franrobots/RescueMaze_FranRobots_WorldWide/Docs/Media/Teamwork_Timeline.png

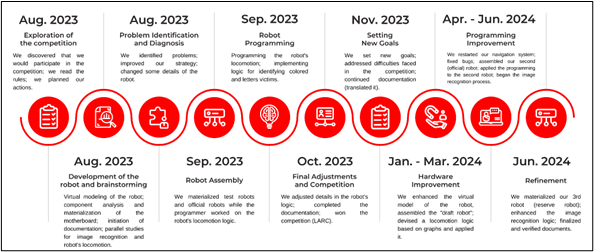
Docs/Media/Teamwork_Timeline.png
