franrobots/RescueMaze_FranRobots_WorldWide/Docs/Media/Trello_Repository.png

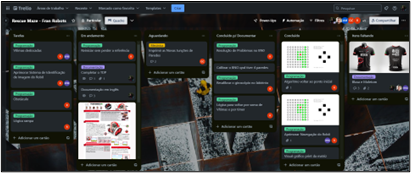
Docs/Media/Trello_Repository.png
