franrobots/RescueMaze_FranRobots_WorldWide/Electronics/Media/MotherBoard/Motherboard_3D_EasyEDA.png

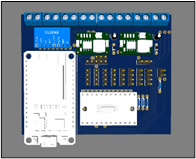
Electronics/Media/MotherBoard/Motherboard_3D_EasyEDA.png
