franrobots/RescueMaze_FranRobots_WorldWide/Electronics/Media/Reflective/Color Sensor Board/3D_Model_ColorSensorBoard.jpeg

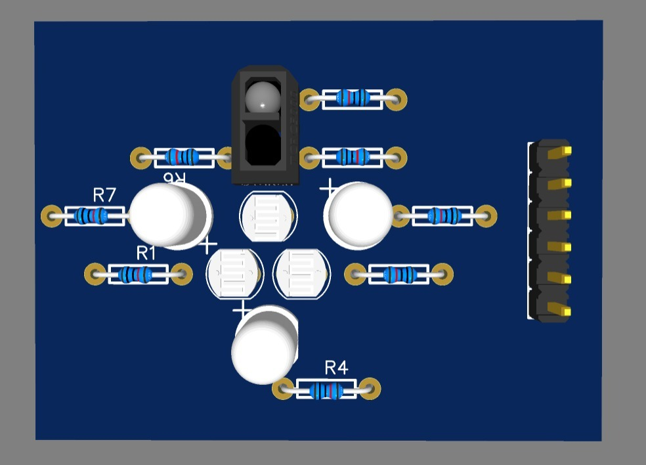
Electronics/Media/Reflective/Color Sensor Board/3D_Model_ColorSensorBoard.jpeg
