franrobots/RescueMaze_FranRobots_WorldWide/Electronics/Media/Reflective/Color Sensor Board/PCB_Layout_ColorSensorBoard.jpeg

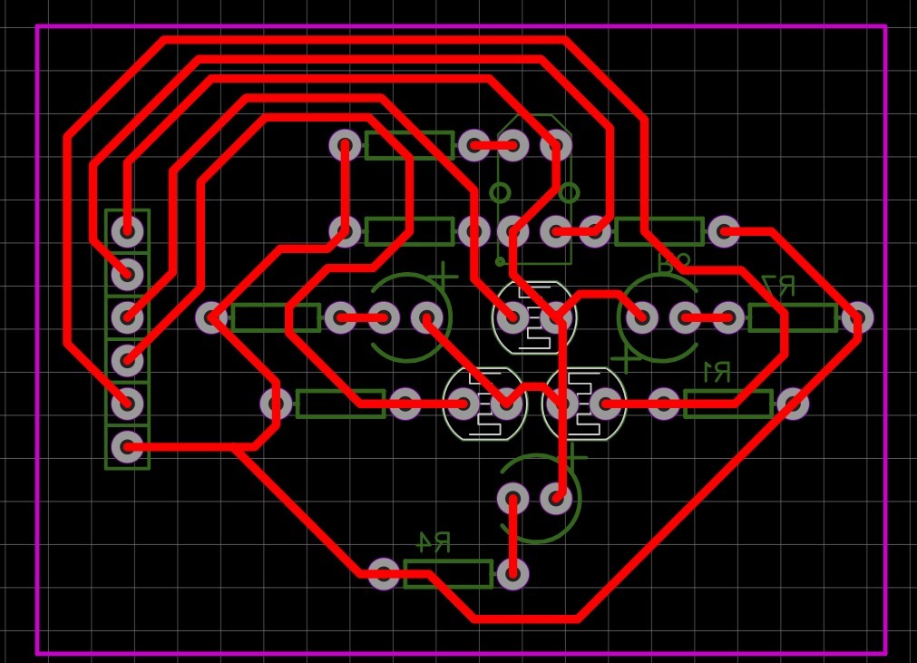
Electronics/Media/Reflective/Color Sensor Board/PCB_Layout_ColorSensorBoard.jpeg
