franrobots/RescueMaze_FranRobots_WorldWide/Mechanics/Media/3D/Anti-Rollover_Part.jpeg

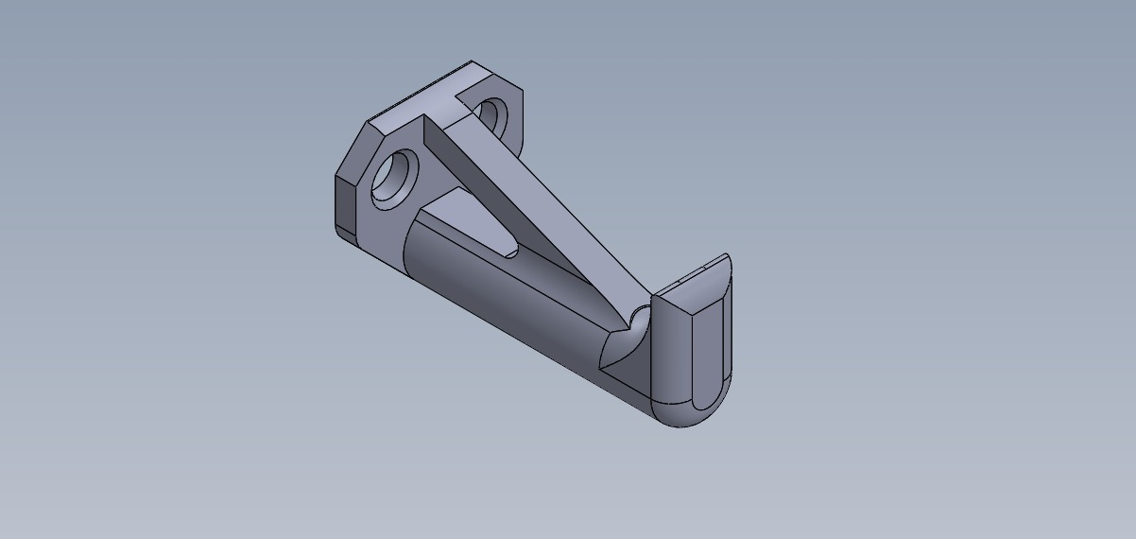
Mechanics/Media/3D/Anti-Rollover_Part.jpeg
