franrobots/RescueMaze_FranRobots_WorldWide/Mechanics/Media/Ilustrations/CrankShaftMechanism_Ilustration.jpg

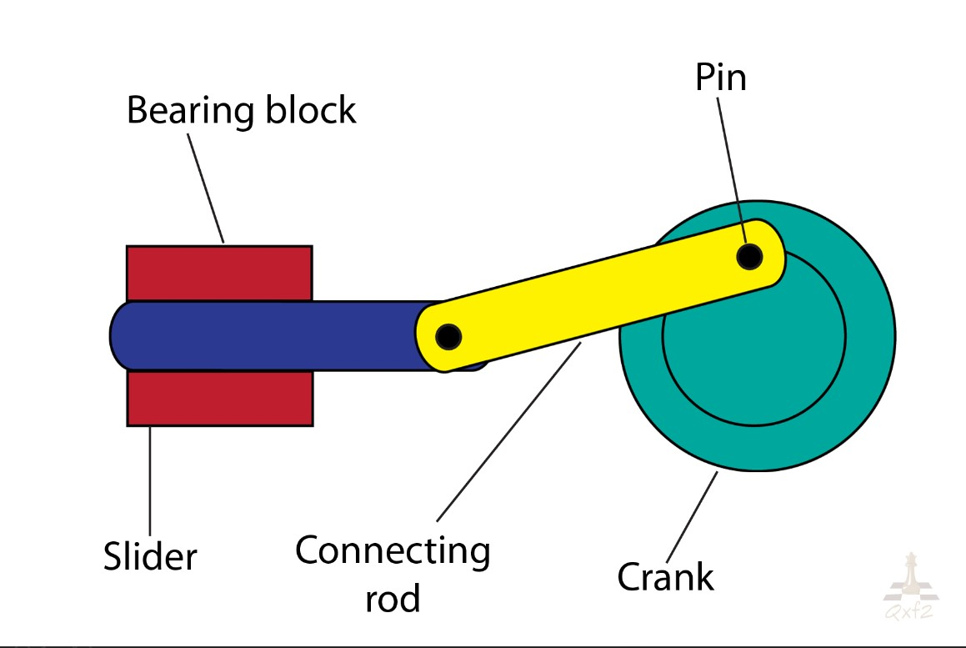
Mechanics/Media/Ilustrations/CrankShaftMechanism_Ilustration.jpg
