franrobots/RescueMaze_FranRobots_WorldWide/Mechanics/Media/Ilustrations/Trigger_Diagram.png

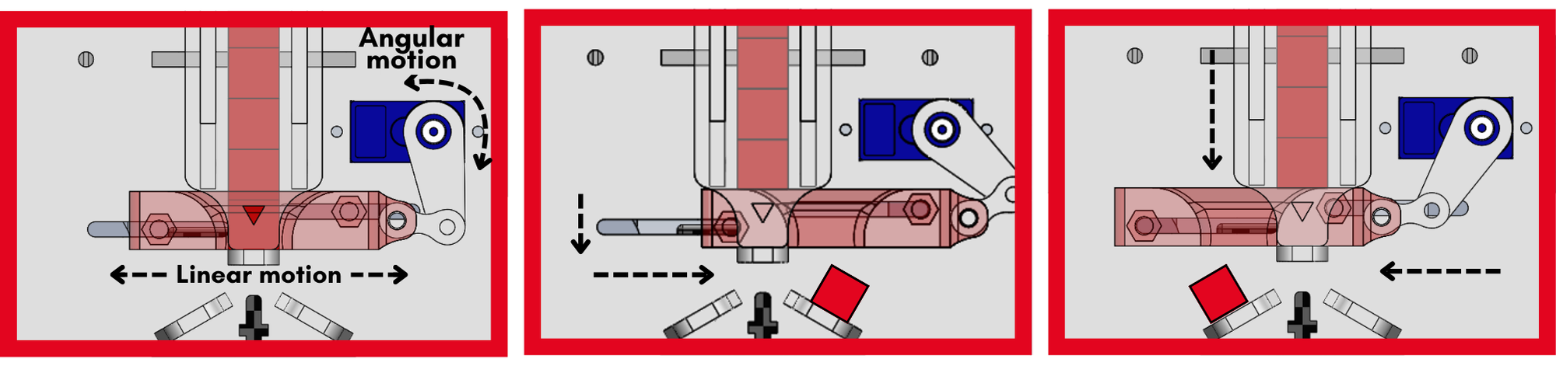
Mechanics/Media/Ilustrations/Trigger_Diagram.png
