franrobots/RescueMaze_FranRobots_WorldWide/Mechanics/Renderings/MazeRobot_Isometric_Back Render 3840x2160.JPG

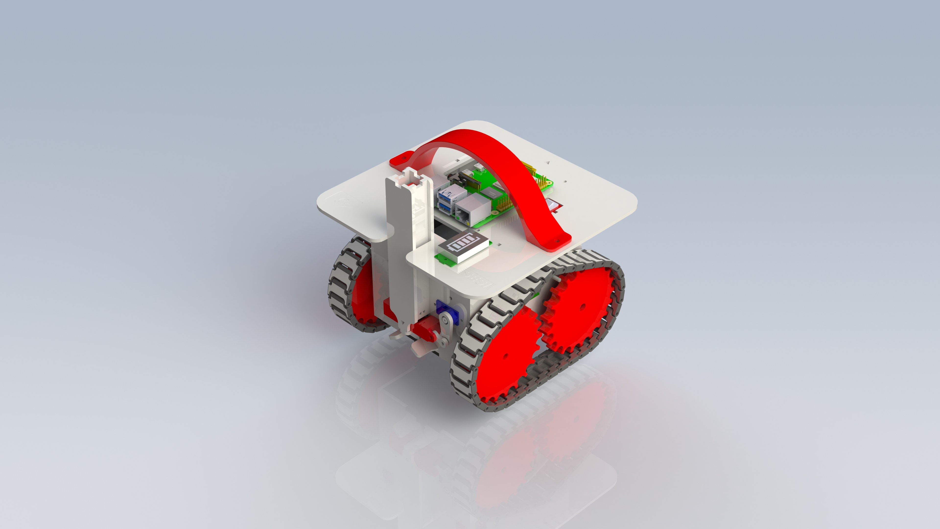
Mechanics/Renderings/MazeRobot_Isometric_Back Render 3840x2160.JPG
