franrobots/RescueMaze_FranRobots_WorldWide/Mechanics/Renderings/MazeRobot_Isometric_Front Render 3840x2160.JPG

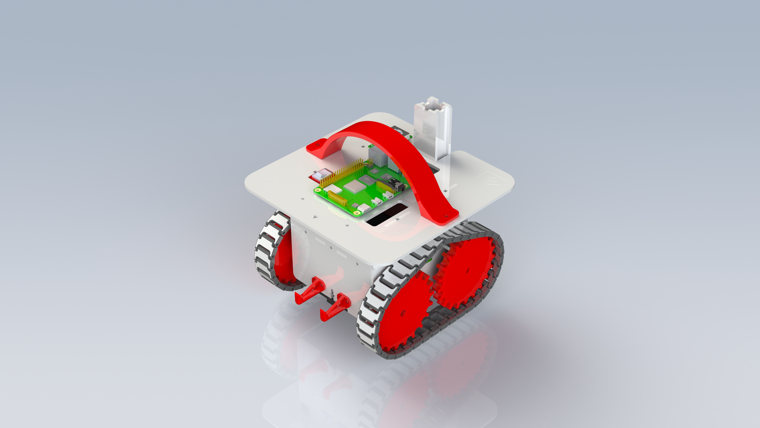
Mechanics/Renderings/MazeRobot_Isometric_Front Render 3840x2160.JPG
