franrobots/RescueMaze_FranRobots_WorldWide/Mechanics/Renderings/MazeRobot_Side Render 3840x2160.JPG

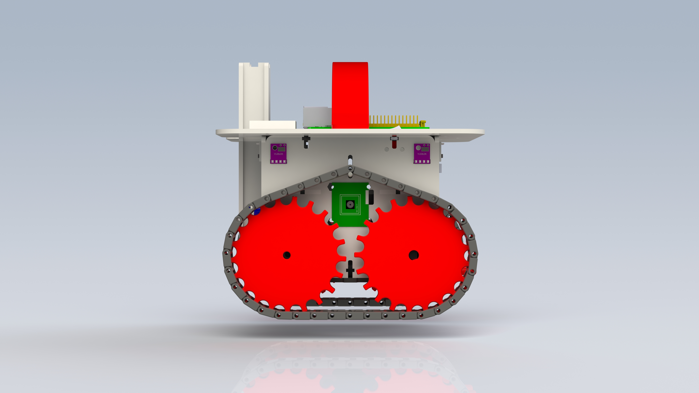
Mechanics/Renderings/MazeRobot_Side Render 3840x2160.JPG
