franrobots/RescueMaze_FranRobots_WorldWide/Programming/Media/Flowcharts/Flowchart_analysis_of_tile_colors__decision_process__action_taking.png

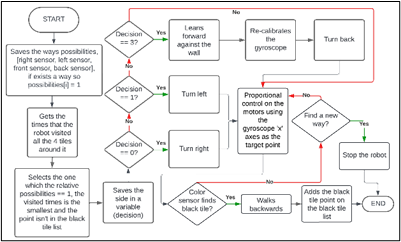
Programming/Media/Flowcharts/Flowchart_analysis_of_tile_colors__decision_process__action_taking.png
