franrobots/RescueMaze_FranRobots_WorldWide/Programming/Media/Flowcharts/Flowchart_interruption_process.png

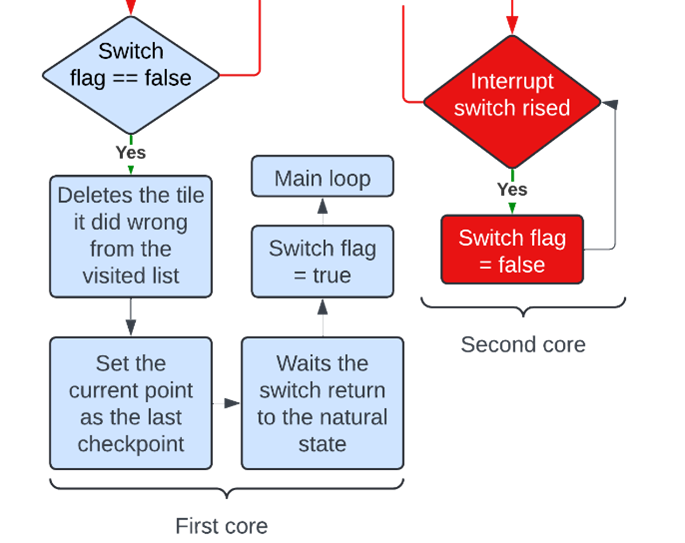
Programming/Media/Flowcharts/Flowchart_interruption_process.png
