franrobots/RescueMaze_FranRobots_WorldWide/Programming/Media/Flowcharts/Flowchart_our_library.png

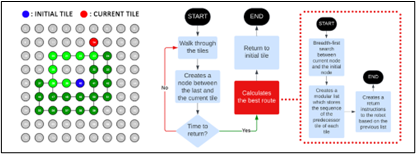
Programming/Media/Flowcharts/Flowchart_our_library.png
