franrobots/RescueMaze_FranRobots_WorldWide/Programming/Media/Flowcharts/Flowchart_victim_segregation_and_classification.png

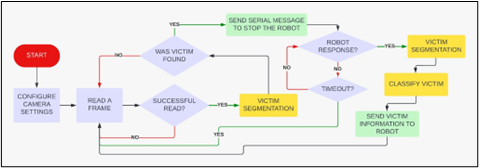
Programming/Media/Flowcharts/Flowchart_victim_segregation_and_classification.png
