franrobots/RescueMaze_FranRobots_WorldWide/Programming/Media/Picture_victim_segregation_and_classification.png

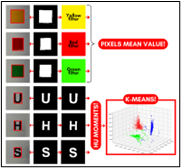
Programming/Media/Picture_victim_segregation_and_classification.png
