franrobots/RescueMaze_FranRobots_WorldWide/Mechanics/3D Printing Prices and Specs./Price and Printing Specs. - 2x Anti-Rollover Parts.png

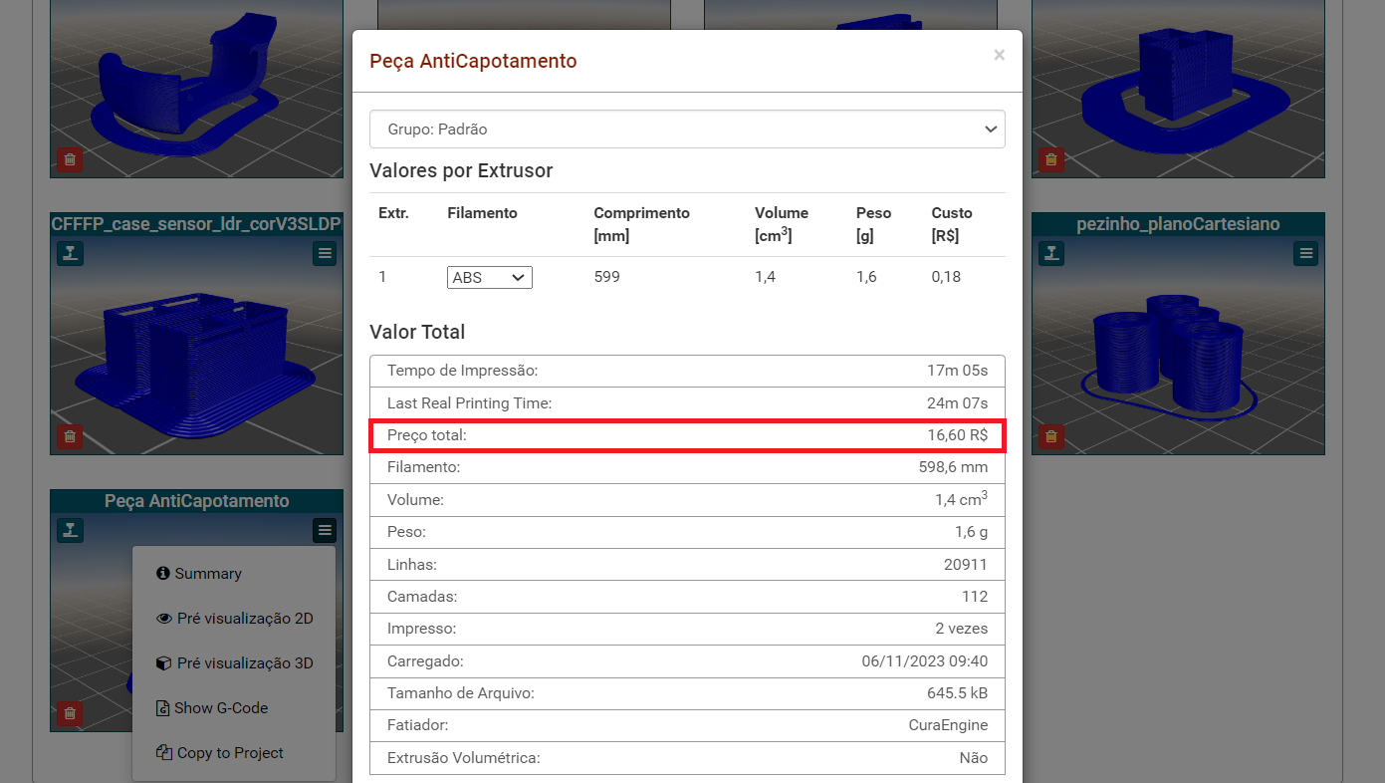
Mechanics/3D Printing Prices and Specs./Price and Printing Specs. - 2x Anti-Rollover Parts.png
