franrobots/RescueMaze_FranRobots_WorldWide/Mechanics/Robot´s 3D Models/Componentes/Parafusos e Porcas/Porcas/Porca M3.STEP

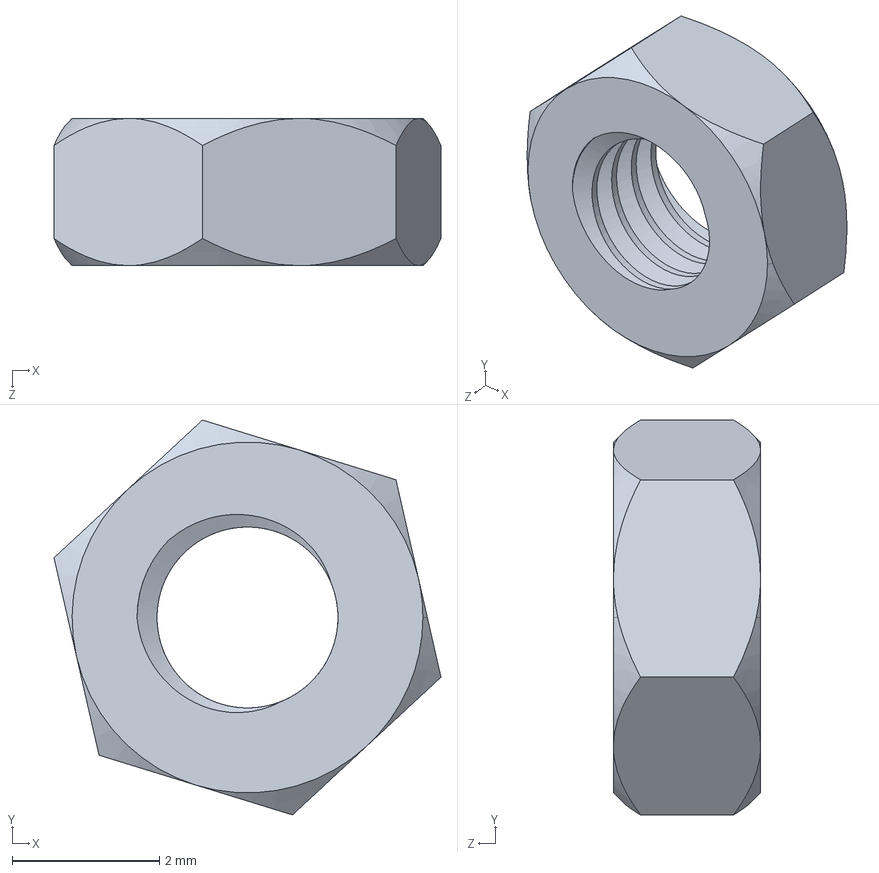
[picture p41: CAD file, 2024-06-11]
Mechanics/Robot´s 3D Models/Componentes/Parafusos e Porcas/Porcas/Porca M3.STEP
5.26 x 5.36 x 2.00 mm
