franrobots/RescueMaze_FranRobots_WorldWide/Mechanics/Robot´s 3D Models/Componentes/Placa de Refletância/Case LDR Tripla.SLDPRT

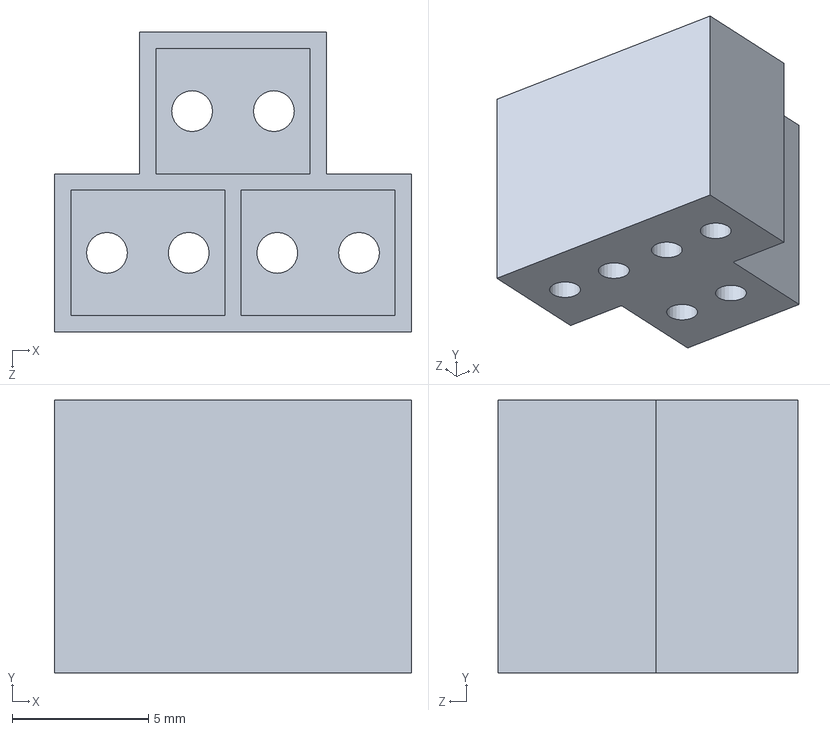
[picture p42: CAD file, 2024-06-19]
Mechanics/Robot´s 3D Models/Componentes/Placa de Refletância/Case LDR Tripla.SLDPRT
13.1 x 10.0 x 11.0 mm
