franrobots/RescueMaze_FranRobots_WorldWide/Mechanics/Robot´s 3D Models/Componentes/Placa Mãe - Robô Maze/Conectores/Barras Pinada Fêmea/19-Pin Header - Female - 2.54mm.STEP

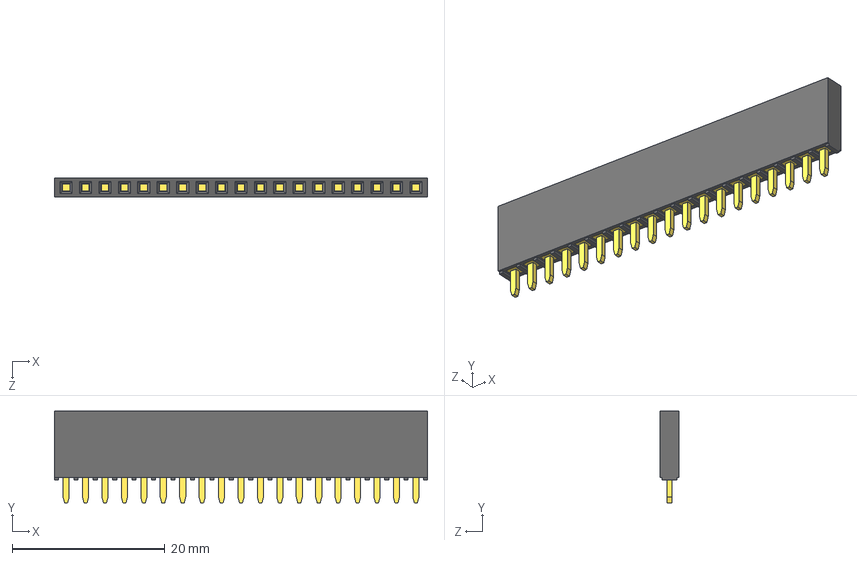
[picture p43: CAD file, 2024-06-19]
Mechanics/Robot´s 3D Models/Componentes/Placa Mãe - Robô Maze/Conectores/Barras Pinada Fêmea/19-Pin Header - Female - 2.54mm.STEP
48.8 x 12.0 x 2.50 mm
