franrobots/RescueMaze_FranRobots_WorldWide/Mechanics/Robot´s 3D Models/Componentes/Placa Mãe - Robô Maze/Conectores/Barras Pinada Macho/1-Pin Header - Male - 2.54mm/1-Pin Header - Male - 2.54mm.STEP

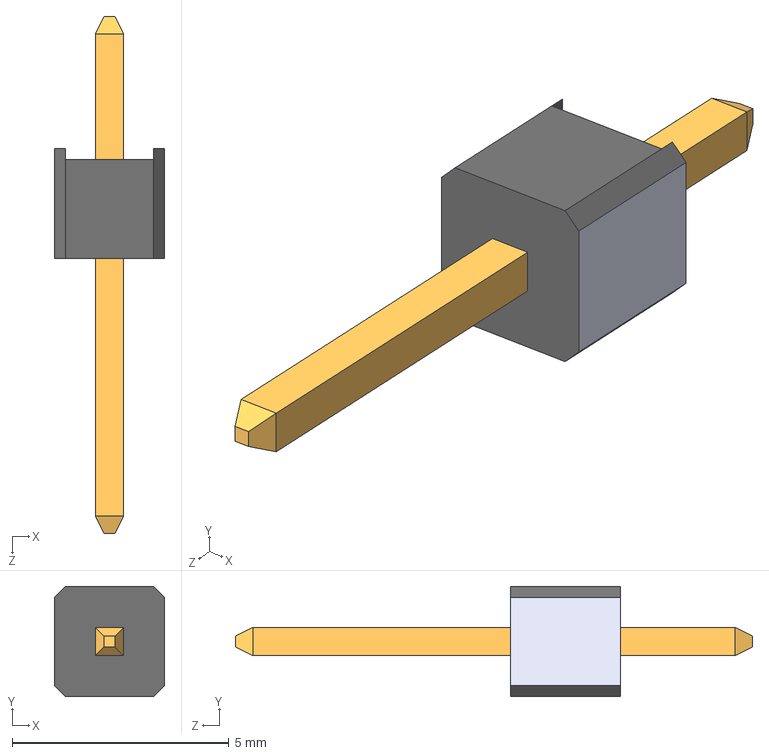
[picture p44: CAD file, 2024-06-11]
Mechanics/Robot´s 3D Models/Componentes/Placa Mãe - Robô Maze/Conectores/Barras Pinada Macho/1-Pin Header - Male - 2.54mm/1-Pin Header - Male - 2.54mm.STEP
2.54 x 2.54 x 11.9 mm
