franrobots/RescueMaze_FranRobots_WorldWide/Mechanics/Robot´s 3D Models/Componentes/Placa Mãe - Robô Maze/Conectores/Barras Pinada Macho/3-Pin Header - Male - 2.54mm.step

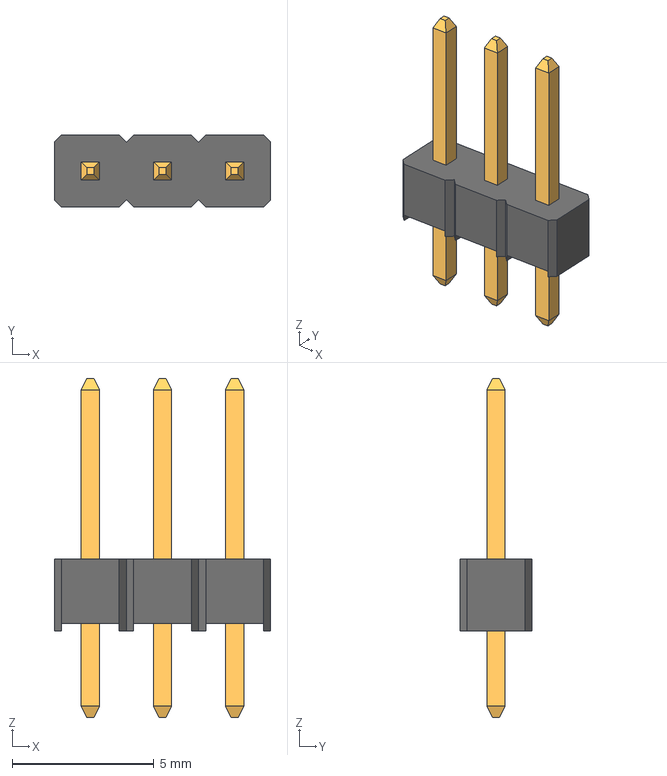
[picture p45: CAD file, 2024-06-11]
Mechanics/Robot´s 3D Models/Componentes/Placa Mãe - Robô Maze/Conectores/Barras Pinada Macho/3-Pin Header - Male - 2.54mm.step
7.62 x 2.54 x 11.9 mm
