franrobots/RescueMaze_FranRobots_WorldWide/Mechanics/Robot´s 3D Models/Componentes/Placa Mãe - Robô Maze/Conectores/Bornes/2 PIN - DG306-5 - PITCH 5 mm.stp

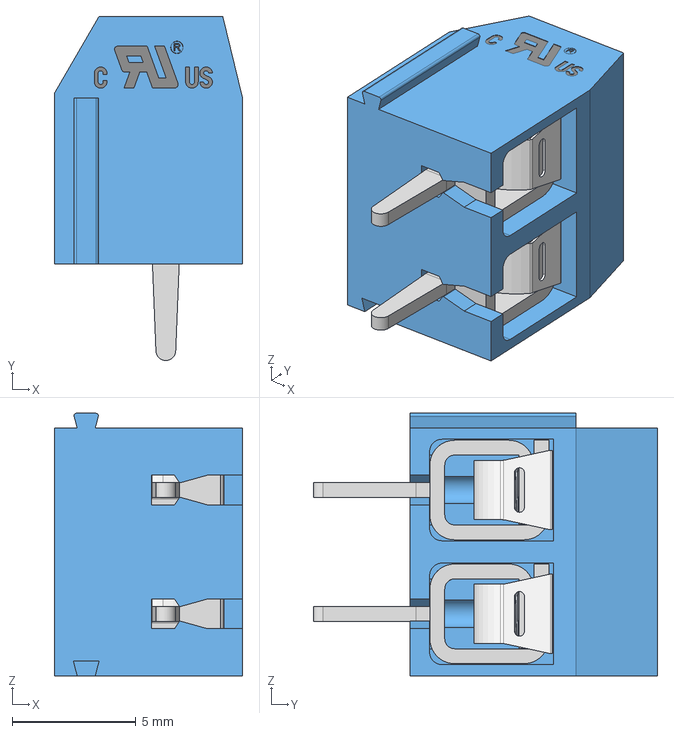
[picture p46: CAD file, 2024-06-19]
Mechanics/Robot´s 3D Models/Componentes/Placa Mãe - Robô Maze/Conectores/Bornes/2 PIN - DG306-5 - PITCH 5 mm.stp
7.60 x 13.9 x 10.6 mm
