franrobots/RescueMaze_FranRobots_WorldWide/Mechanics/Robot´s 3D Models/Componentes/Placa Mãe - Robô Maze/Placa Ilhada 90x70.SLDPRT

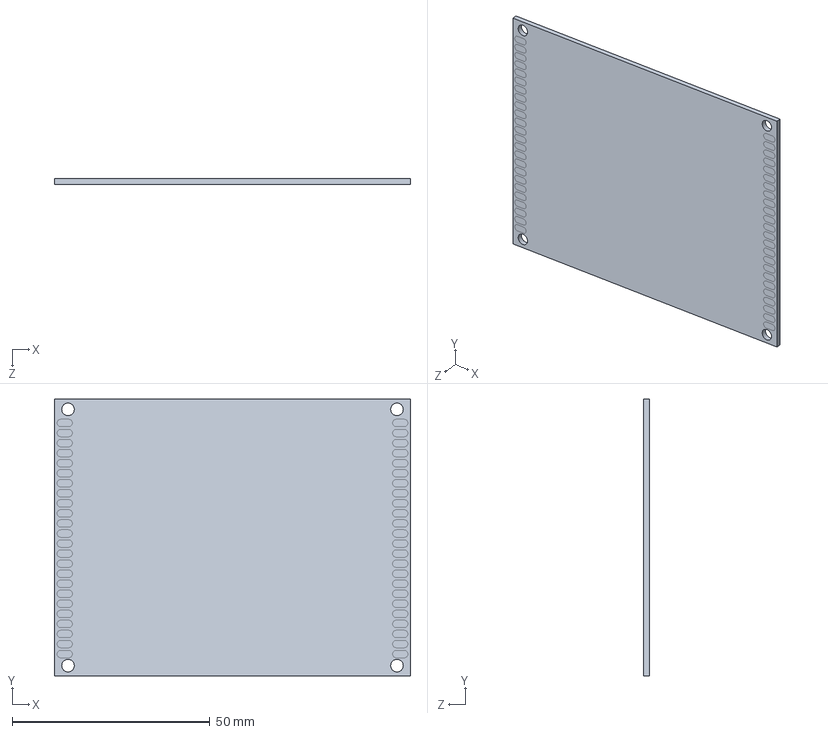
[picture p47: CAD file, 2024-06-19]
Mechanics/Robot´s 3D Models/Componentes/Placa Mãe - Robô Maze/Placa Ilhada 90x70.SLDPRT
90.0 x 70.0 x 1.42 mm
