franrobots/RescueMaze_FranRobots_WorldWide/Mechanics/Robot´s 3D Models/Componentes/Servo Motor/SG90 - Micro Servo 9g - Tower Pro.SLDPRT

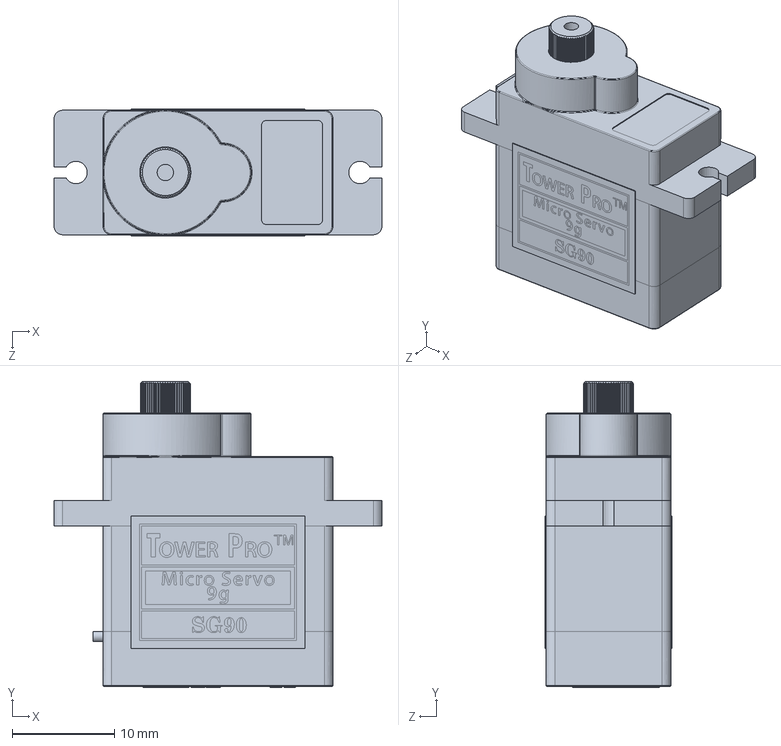
[picture p48: CAD file, 2024-06-19]
Mechanics/Robot´s 3D Models/Componentes/Servo Motor/SG90 - Micro Servo 9g - Tower Pro.SLDPRT
32.1 x 30.0 x 12.4 mm
