franrobots/RescueMaze_FranRobots_WorldWide/Mechanics/Robot´s 3D Models/Componentes/Switchs/tugas uts rocker switch.SLDPRT

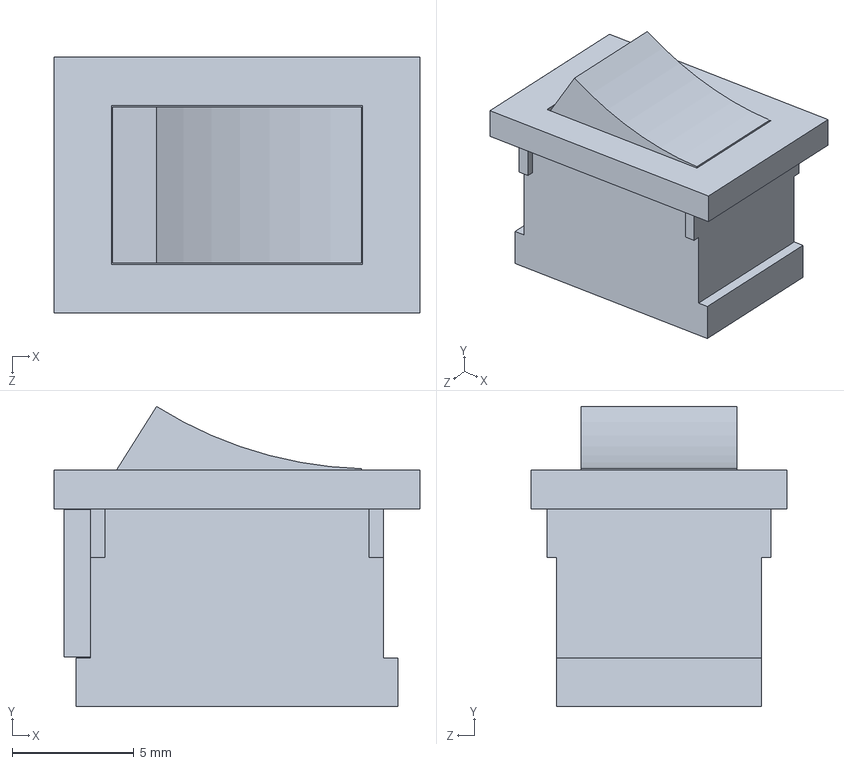
[picture p49: CAD file, 2024-06-19]
Mechanics/Robot´s 3D Models/Componentes/Switchs/tugas uts rocker switch.SLDPRT
15.0 x 12.3 x 10.5 mm
