franrobots/RescueMaze_FranRobots_WorldWide/Mechanics/Robot´s 3D Models/Disparador/Disparador Tapete/Conector Servo Manivela.SLDPRT

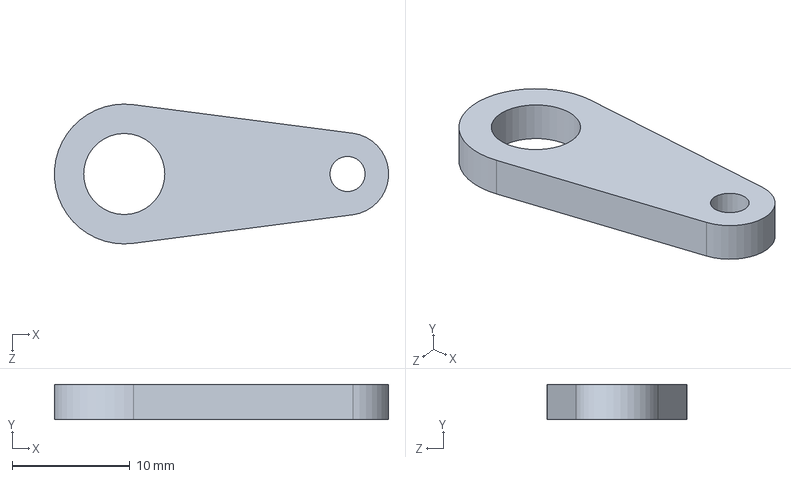
[picture p50: CAD file, 2024-06-19]
Mechanics/Robot´s 3D Models/Disparador/Disparador Tapete/Conector Servo Manivela.SLDPRT
28.4 x 3.00 x 11.9 mm
