franrobots/RescueMaze_FranRobots_WorldWide/Mechanics/Robot´s 3D Models/Disparador/Estoque Disparador/Parede Traseira - Estoque Disparador.SLDPRT

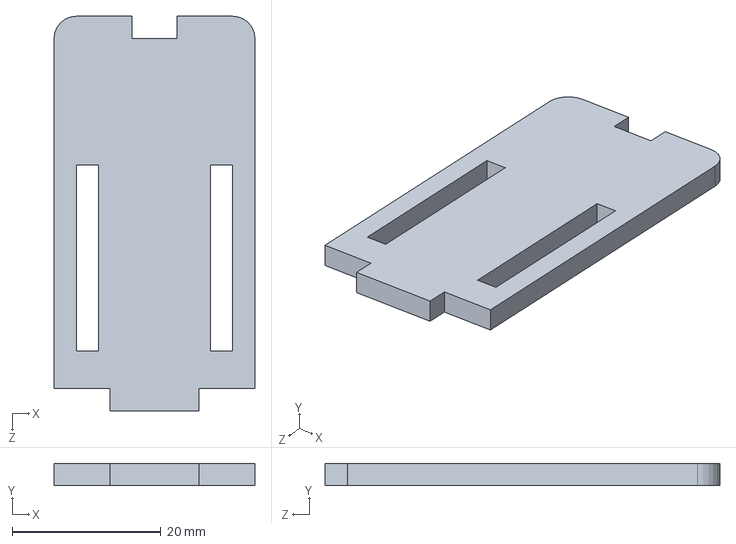
[picture p51: CAD file, 2024-06-19]
Mechanics/Robot´s 3D Models/Disparador/Estoque Disparador/Parede Traseira - Estoque Disparador.SLDPRT
27.0 x 3.00 x 53.0 mm
