franrobots/RescueMaze_FranRobots_WorldWide/Mechanics/Robot´s 3D Models/Disparador/Extensor Estoque Kits.SLDPRT

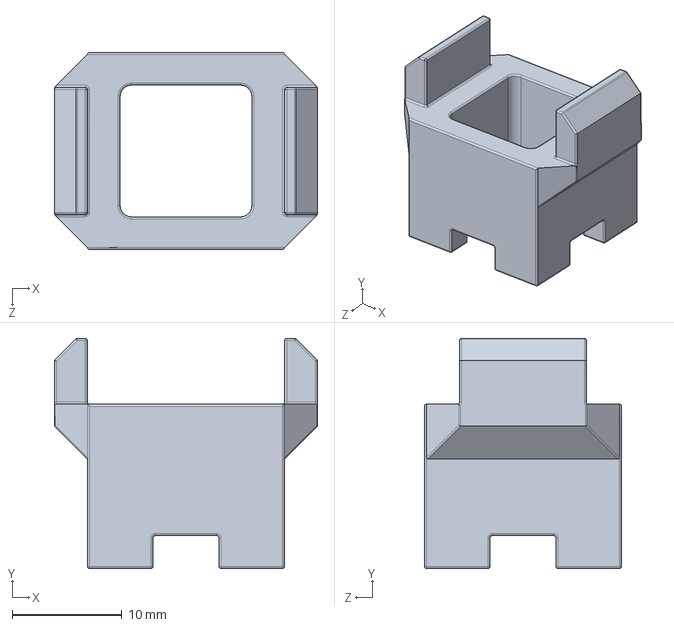
[picture p52: CAD file, 2024-06-11]
Mechanics/Robot´s 3D Models/Disparador/Extensor Estoque Kits.SLDPRT
24.0 x 21.0 x 18.0 mm
