franrobots/RescueMaze_FranRobots_WorldWide/Mechanics/Robot´s 3D Models/Lateral Direita - Maze.SLDPRT

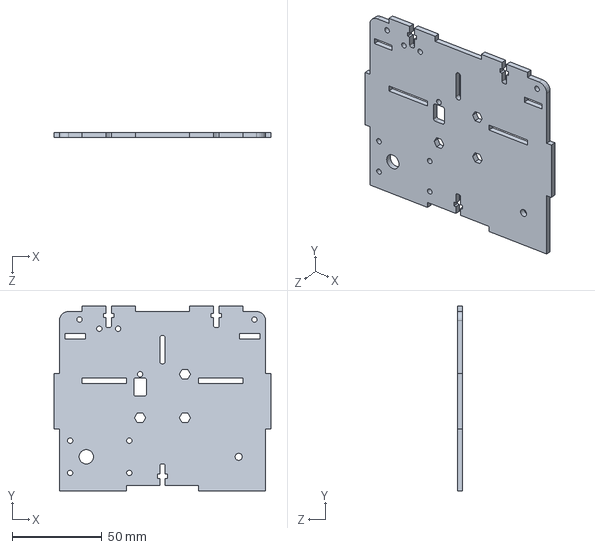
[picture p53: CAD file, 2024-06-21]
Mechanics/Robot´s 3D Models/Lateral Direita - Maze.SLDPRT
121.0 x 103.0 x 3.00 mm
