franrobots/RescueMaze_FranRobots_WorldWide/Mechanics/Robot´s 3D Models/Pista/Kit de Resgate.SLDPRT

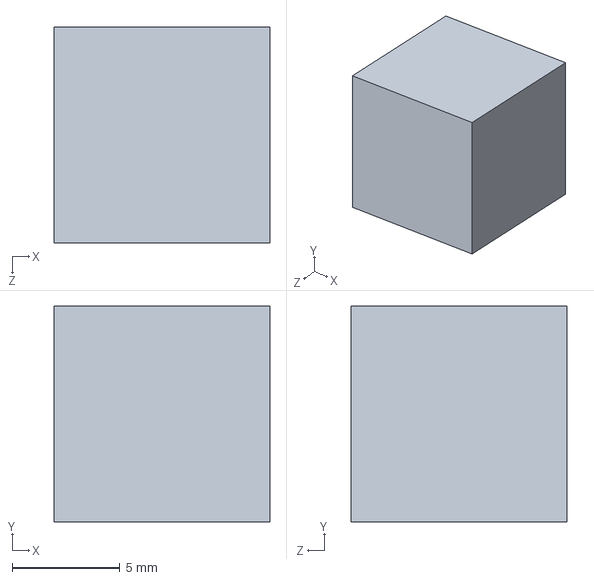
[picture p54: CAD file, 2024-06-19]
Mechanics/Robot´s 3D Models/Pista/Kit de Resgate.SLDPRT
10.0 x 10.0 x 10.0 mm
