franrobots/RescueMaze_FranRobots_WorldWide/Mechanics/Robot´s 3D Models/Rodas e esteiras/Dentes Esteira/Dente Esteira - Engrenagem.SLDPRT

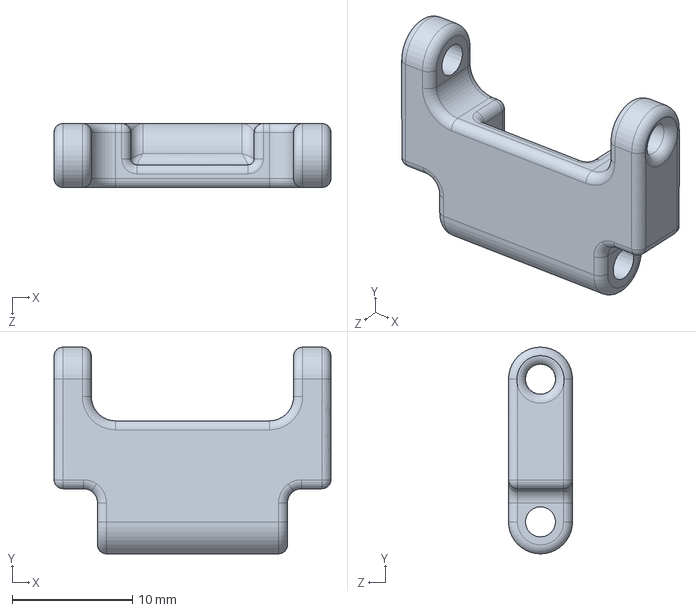
[picture p55: CAD file, 2024-06-19]
Mechanics/Robot´s 3D Models/Rodas e esteiras/Dentes Esteira/Dente Esteira - Engrenagem.SLDPRT
23.0 x 17.2 x 5.32 mm
