franrobots/RescueMaze_FranRobots_WorldWide/Mechanics/Robot´s 3D Models/Rodas e esteiras/Rodas/7988 - Atual/Engrenagem Movida Reduzida - Passo 11,92 7988.SLDPRT

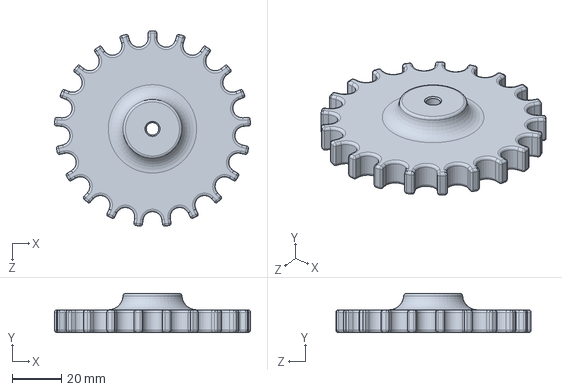
[picture p56: CAD file, 2024-06-19]
Mechanics/Robot´s 3D Models/Rodas e esteiras/Rodas/7988 - Atual/Engrenagem Movida Reduzida - Passo 11,92 7988.SLDPRT
79.8 x 15.9 x 79.6 mm
