franrobots/RescueMaze_FranRobots_WorldWide/Mechanics/Robot´s 3D Models/Componentes/Bateria/PDB XT60 PLUG.SLDPRT

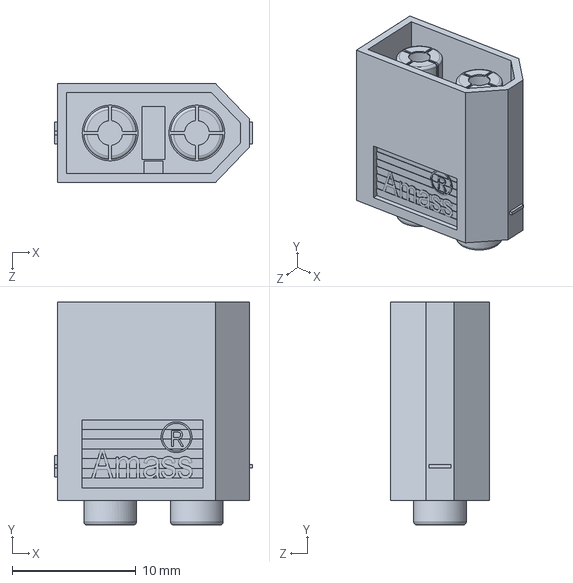
[picture p57: CAD file, 2024-06-11]
Mechanics/Robot´s 3D Models/Componentes/Bateria/PDB XT60 PLUG.SLDPRT
16.0 x 18.0 x 8.00 mm
