franrobots/RescueMaze_FranRobots_WorldWide/Mechanics/Robot´s 3D Models/Componentes/Câmera/Raspberry Cam.step

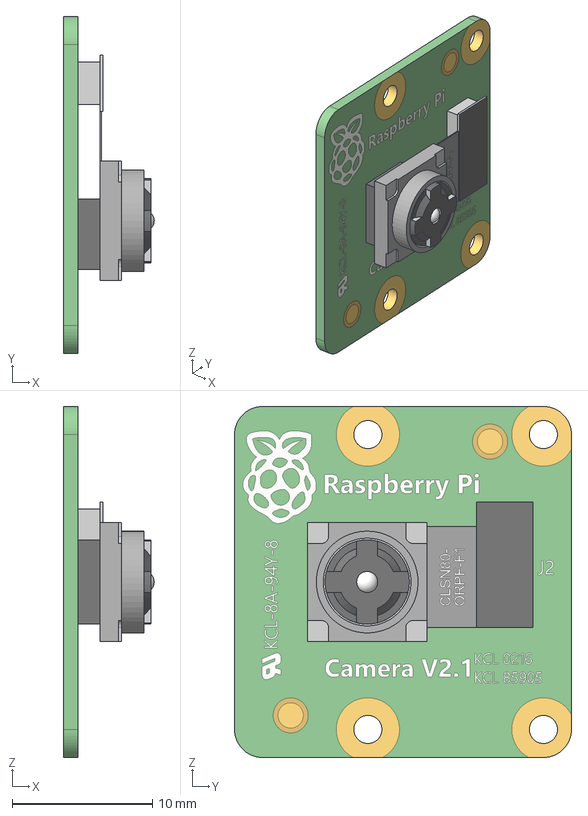
[picture p58: CAD file, 2024-06-11]
Mechanics/Robot´s 3D Models/Componentes/Câmera/Raspberry Cam.step
6.45 x 24.0 x 25.0 mm
