franrobots/RescueMaze_FranRobots_WorldWide/Mechanics/Robot´s 3D Models/Componentes/Encoder/Encoder Original/Encoder Motor.SLDPRT

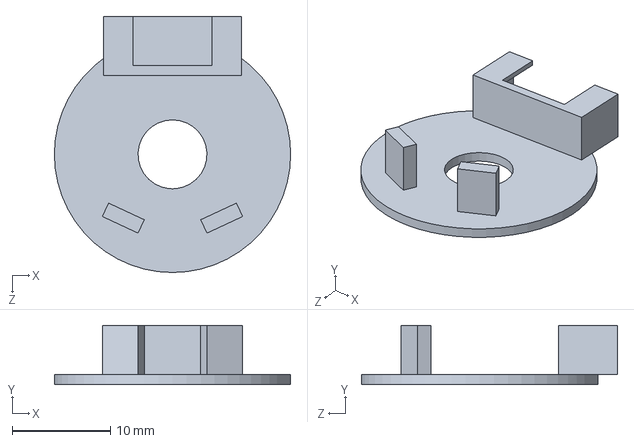
[picture p59: CAD file, 2024-06-19]
Mechanics/Robot´s 3D Models/Componentes/Encoder/Encoder Original/Encoder Motor.SLDPRT
24.0 x 6.00 x 26.0 mm
