franrobots/RescueMaze_FranRobots_WorldWide/Mechanics/Robot´s 3D Models/Componentes/GY-VL53/Adaptador GY_VL53 LDK-1XV2.SLDPRT

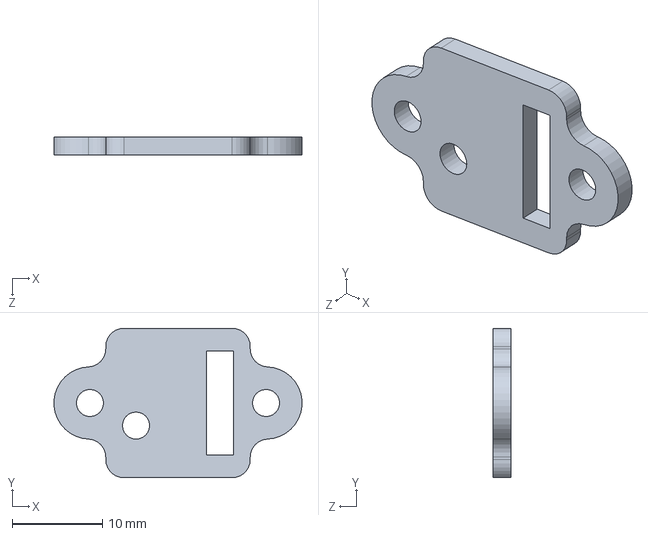
[picture p60: CAD file, 2024-06-19]
Mechanics/Robot´s 3D Models/Componentes/GY-VL53/Adaptador GY_VL53 LDK-1XV2.SLDPRT
27.5 x 16.6 x 2.00 mm
