franrobots/RescueMaze_FranRobots_WorldWide/Mechanics/Robot´s 3D Models/Componentes/Motor DC - MJ TEK8 - 12v 100 RPM.SLDPRT

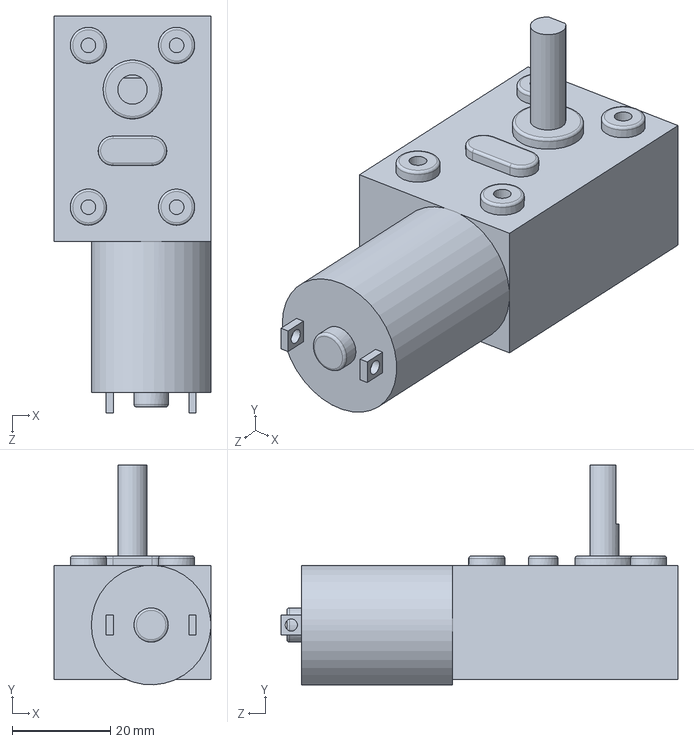
[picture p61: CAD file, 2024-06-19]
Mechanics/Robot´s 3D Models/Componentes/Motor DC - MJ TEK8 - 12v 100 RPM.SLDPRT
32.0 x 44.8 x 81.0 mm
