franrobots/RescueMaze_FranRobots_WorldWide/Mechanics/Robot´s 3D Models/Componentes/Parafusos e Porcas/Arruelas/Arruela M3.SLDPRT

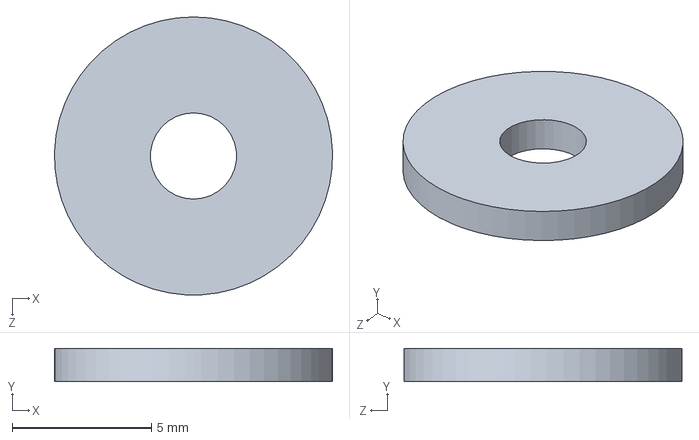
[picture p62: CAD file, 2024-06-19]
Mechanics/Robot´s 3D Models/Componentes/Parafusos e Porcas/Arruelas/Arruela M3.SLDPRT
10.00 x 1.20 x 10.0 mm
