franrobots/RescueMaze_FranRobots_WorldWide/Mechanics/Robot´s 3D Models/Componentes/Parafusos e Porcas/Parafusos/Parafuso M3 Fuso.SLDPRT

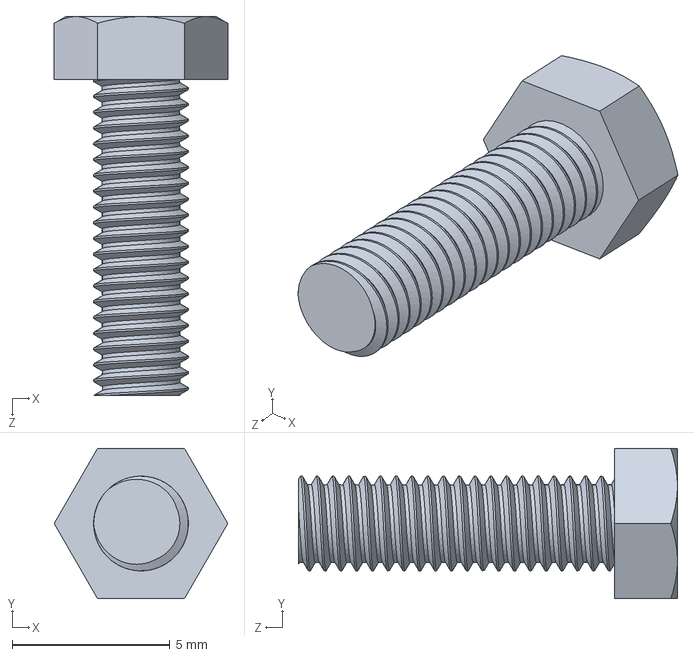
[picture p63: CAD file, 2024-06-11]
Mechanics/Robot´s 3D Models/Componentes/Parafusos e Porcas/Parafusos/Parafuso M3 Fuso.SLDPRT
5.50 x 4.76 x 12.0 mm
