franrobots/RescueMaze_FranRobots_WorldWide/Mechanics/Robot´s 3D Models/Componentes/Parafusos e Porcas/Porcas/Porca M4.stp

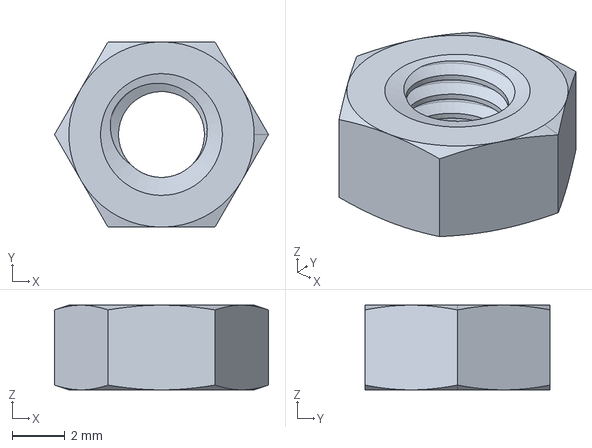
[picture p64: CAD file, 2024-06-11]
Mechanics/Robot´s 3D Models/Componentes/Parafusos e Porcas/Porcas/Porca M4.stp
8.08 x 7.00 x 3.20 mm
