franrobots/RescueMaze_FranRobots_WorldWide/Mechanics/Robot´s 3D Models/Componentes/Placa de Refletância/Case LDR Dupla.SLDPRT

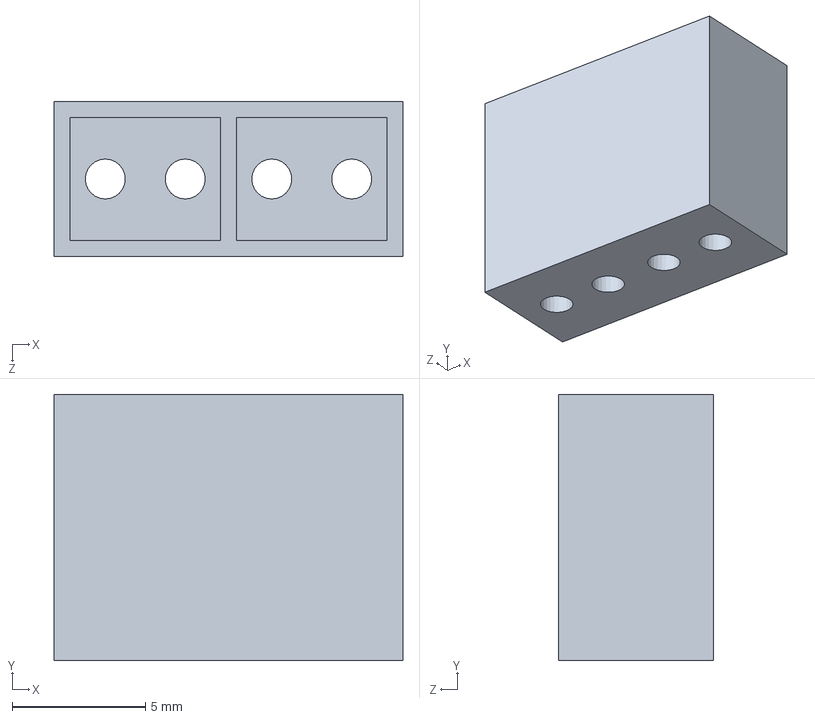
[picture p65: CAD file, 2024-06-14]
Mechanics/Robot´s 3D Models/Componentes/Placa de Refletância/Case LDR Dupla.SLDPRT
13.1 x 10.0 x 5.80 mm
