franrobots/RescueMaze_FranRobots_WorldWide/Mechanics/Robot´s 3D Models/Componentes/Placa Mãe - Robô Maze/Conectores/Barras Pinada Fêmea/15-Pin Header - Female - 2.54mm.step

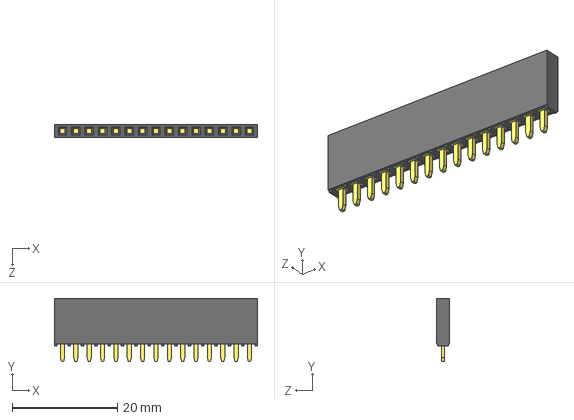
[picture p66: CAD file, 2024-06-19]
Mechanics/Robot´s 3D Models/Componentes/Placa Mãe - Robô Maze/Conectores/Barras Pinada Fêmea/15-Pin Header - Female - 2.54mm.step
38.6 x 12.0 x 2.50 mm
