franrobots/RescueMaze_FranRobots_WorldWide/Mechanics/Robot´s 3D Models/Componentes/Servo Motor/Aleta Micro Servo - Tower Pro.SLDPRT

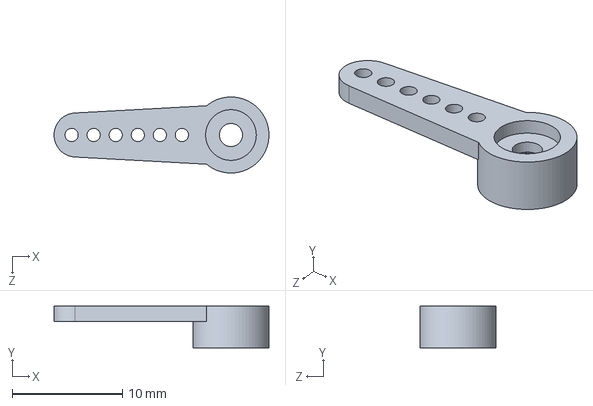
[picture p69: CAD file, 2024-06-11]
Mechanics/Robot´s 3D Models/Componentes/Servo Motor/Aleta Micro Servo - Tower Pro.SLDPRT
19.5 x 3.80 x 6.90 mm
