franrobots/RescueMaze_FranRobots_WorldWide/Mechanics/Robot´s 3D Models/Componentes/Switchs/3D/Suporte Switch.SLDPRT

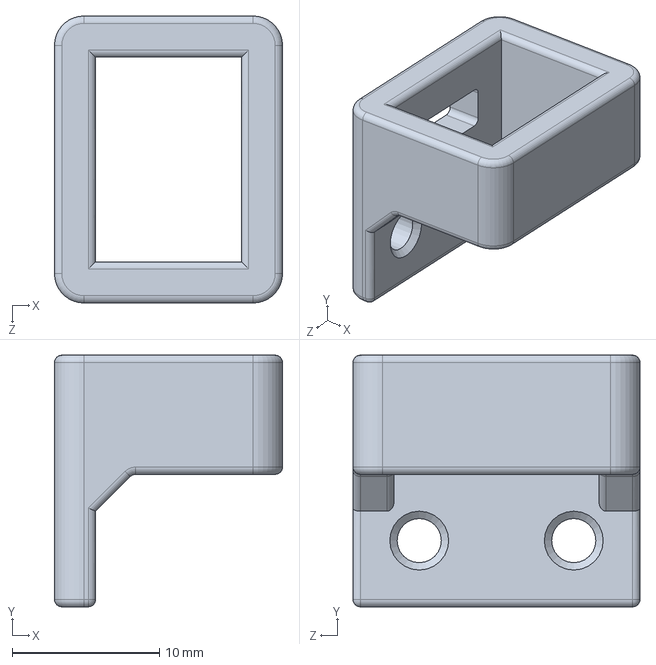
[picture p70: CAD file, 2024-06-19]
Mechanics/Robot´s 3D Models/Componentes/Switchs/3D/Suporte Switch.SLDPRT
15.5 x 17.1 x 19.5 mm
