franrobots/RescueMaze_FranRobots_WorldWide/Mechanics/Robot´s 3D Models/Componentes/Switchs/RockerSwitch.SLDPRT

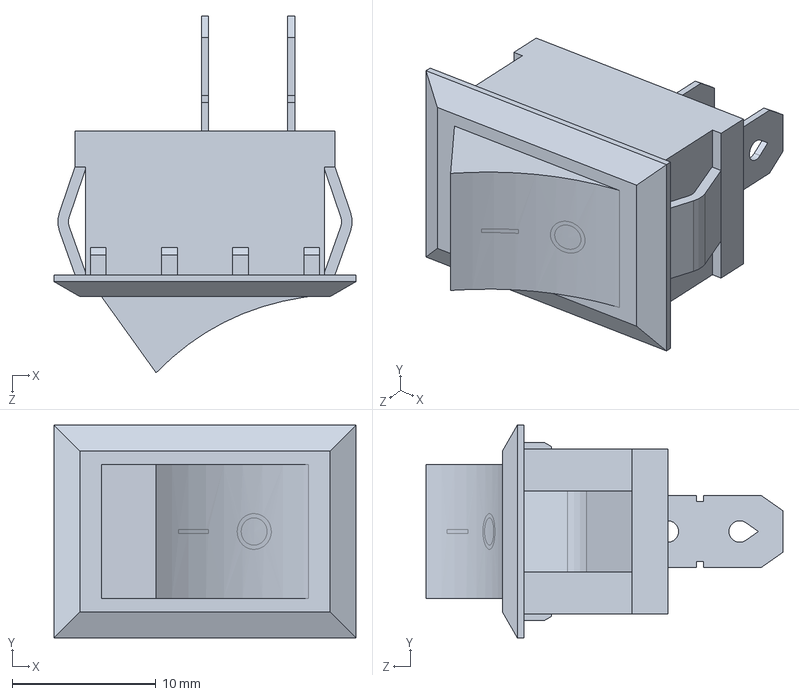
[picture p71: CAD file, 2024-06-11]
Mechanics/Robot´s 3D Models/Componentes/Switchs/RockerSwitch.SLDPRT
21.0 x 14.8 x 24.8 mm
