franrobots/RescueMaze_FranRobots_WorldWide/Mechanics/Robot´s 3D Models/Disparador/Disparador Tapete/Parede Inclinada - Disparador.SLDPRT

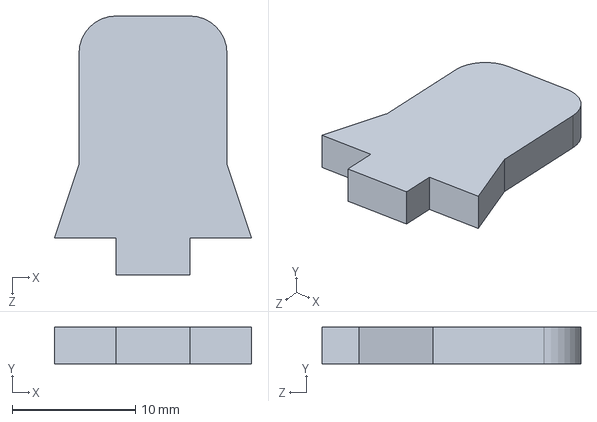
[picture p72: CAD file, 2024-06-19]
Mechanics/Robot´s 3D Models/Disparador/Disparador Tapete/Parede Inclinada - Disparador.SLDPRT
16.0 x 3.00 x 21.0 mm
