franrobots/RescueMaze_FranRobots_WorldWide/Mechanics/Robot´s 3D Models/Disparador/Estoque Disparador/Parede Baixo - Estoque Disparador.SLDPRT

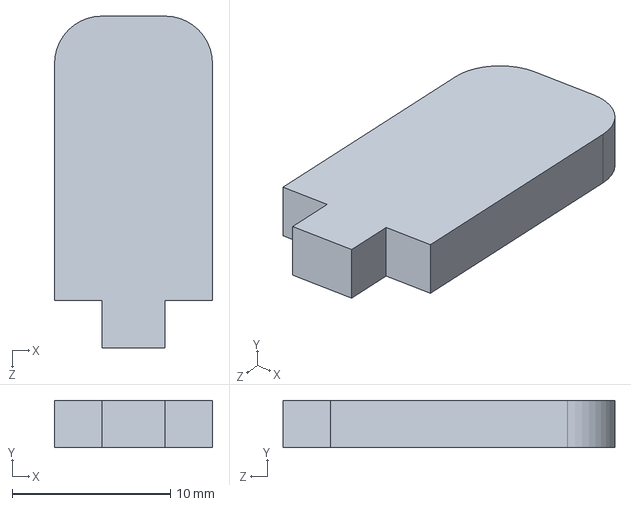
[picture p73: CAD file, 2024-06-19]
Mechanics/Robot´s 3D Models/Disparador/Estoque Disparador/Parede Baixo - Estoque Disparador.SLDPRT
10.0 x 3.00 x 21.0 mm
