franrobots/RescueMaze_FranRobots_WorldWide/Mechanics/Robot´s 3D Models/Rodas e esteiras/Dentes Esteira/Eixo Junção Esteira.SLDPRT

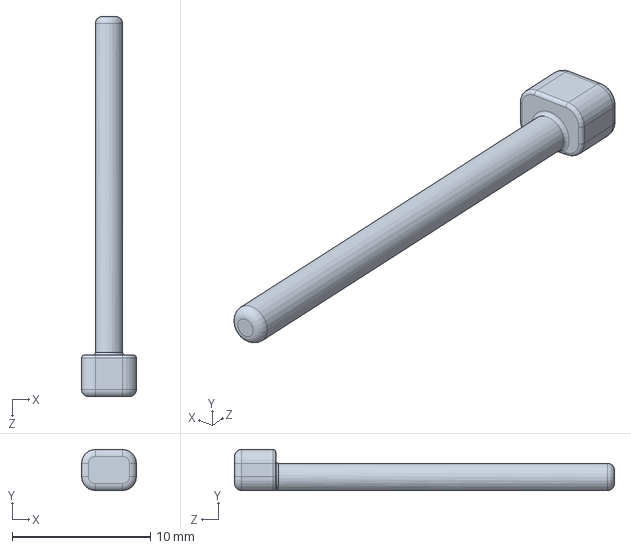
[picture p74: CAD file, 2024-06-19]
Mechanics/Robot´s 3D Models/Rodas e esteiras/Dentes Esteira/Eixo Junção Esteira.SLDPRT
3.97 x 2.97 x 27.5 mm
