franrobots/RescueMaze_FranRobots_WorldWide/Mechanics/Robot´s 3D Models/Rodas e esteiras/Rodas/7988 - Atual/Engrenagem Mov. Red. Encoder - 11,92_7988.SLDPRT

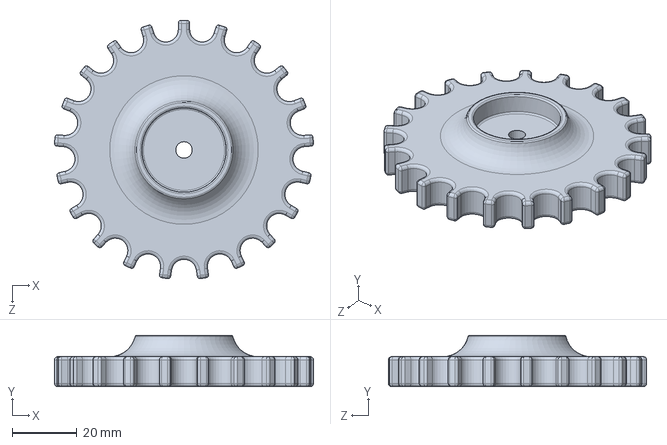
[picture p75: CAD file, 2024-06-19]
Mechanics/Robot´s 3D Models/Rodas e esteiras/Rodas/7988 - Atual/Engrenagem Mov. Red. Encoder - 11,92_7988.SLDPRT
79.8 x 15.8 x 79.6 mm
