franrobots/RescueMaze_FranRobots_WorldWide/Mechanics/Robot´s 3D Models/Componentes/Display Bateria MH-DL18S.SLDPRT

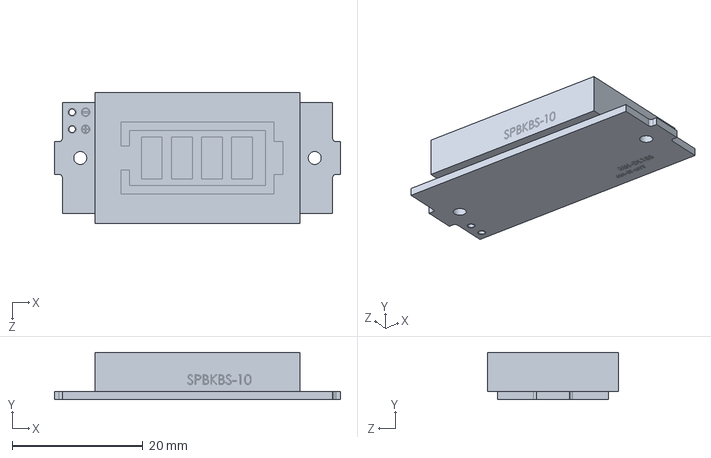
[picture p76: CAD file, 2024-06-19]
Mechanics/Robot´s 3D Models/Componentes/Display Bateria MH-DL18S.SLDPRT
43.8 x 7.20 x 20.0 mm
