franrobots/RescueMaze_FranRobots_WorldWide/Mechanics/Robot´s 3D Models/Componentes/GY-VL53/GY-VL53LDK.SLDPRT

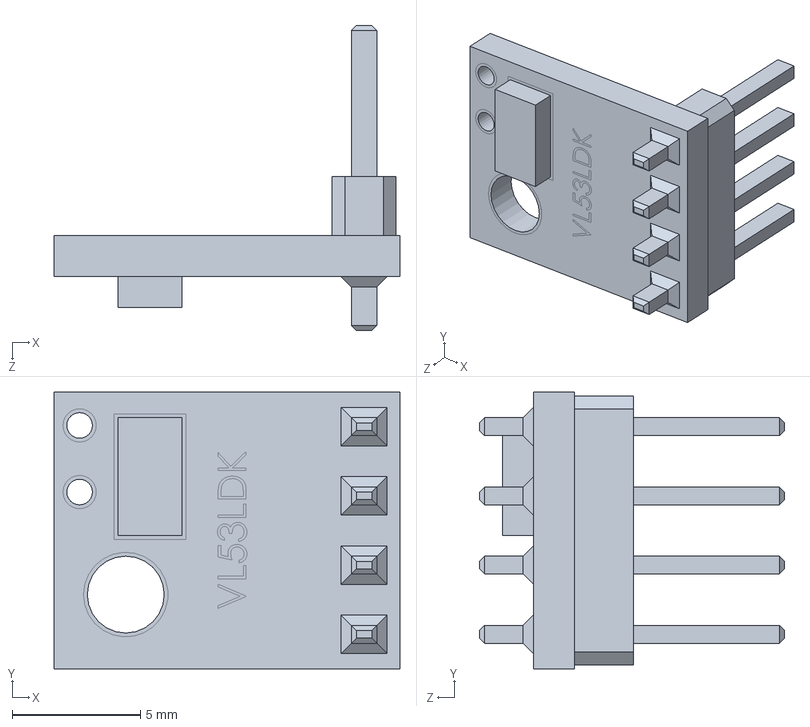
[picture p77: CAD file, 2024-06-19]
Mechanics/Robot´s 3D Models/Componentes/GY-VL53/GY-VL53LDK.SLDPRT
13.5 x 10.8 x 11.9 mm
