franrobots/RescueMaze_FranRobots_WorldWide/Mechanics/Robot´s 3D Models/Componentes/Placa Mãe - Robô Maze/Conectores/Barras Pinada Fêmea/8-Pin Header - Female - 2.54mm.step

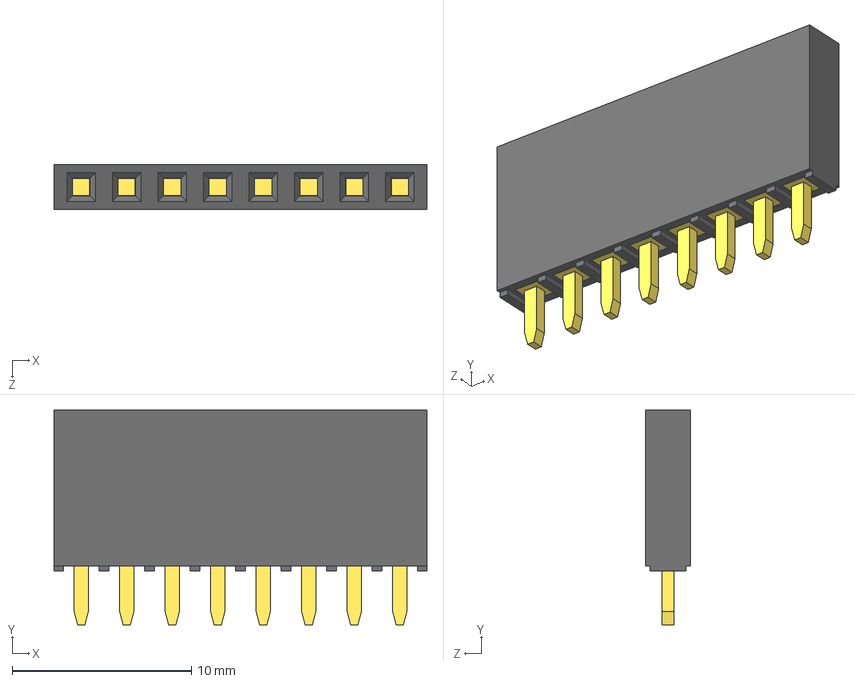
[picture p78: CAD file, 2024-06-11]
Mechanics/Robot´s 3D Models/Componentes/Placa Mãe - Robô Maze/Conectores/Barras Pinada Fêmea/8-Pin Header - Female - 2.54mm.step
20.8 x 12.0 x 2.50 mm
