franrobots/RescueMaze_FranRobots_WorldWide/Mechanics/Robot´s 3D Models/Componentes/Servo Motor/Servo Emax ES08A.SLDPRT

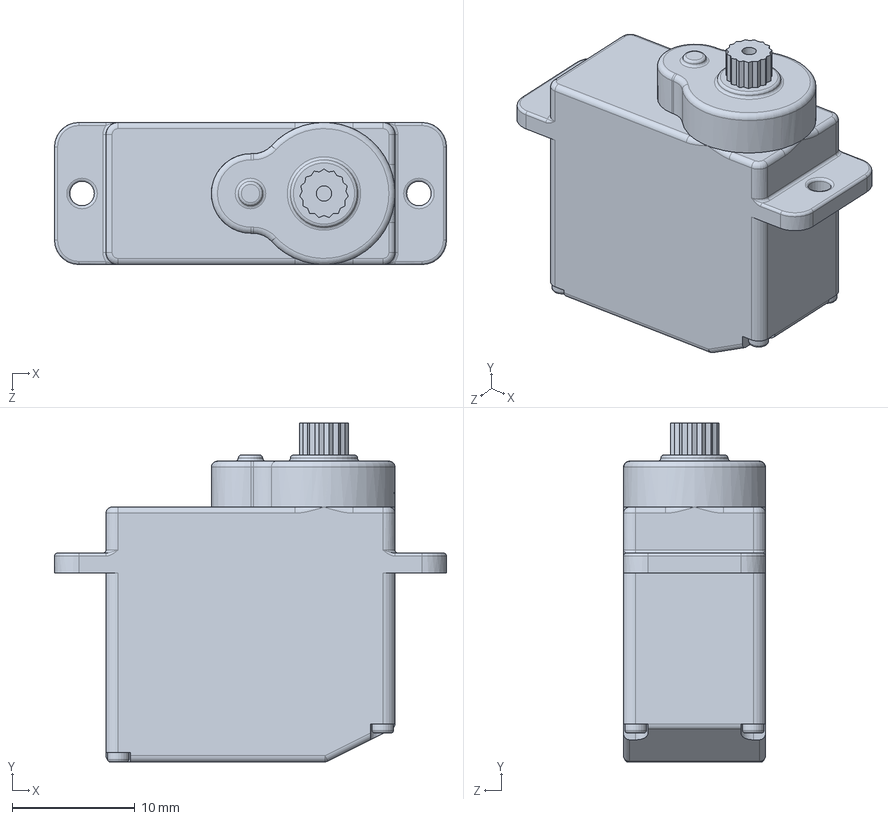
[picture p80: CAD file, 2024-06-11]
Mechanics/Robot´s 3D Models/Componentes/Servo Motor/Servo Emax ES08A.SLDPRT
32.0 x 27.6 x 11.6 mm
