franrobots/RescueMaze_FranRobots_WorldWide/Mechanics/Robot´s 3D Models/Componentes/Switchs/Microswitch KW11-3Z-3.SLDPRT

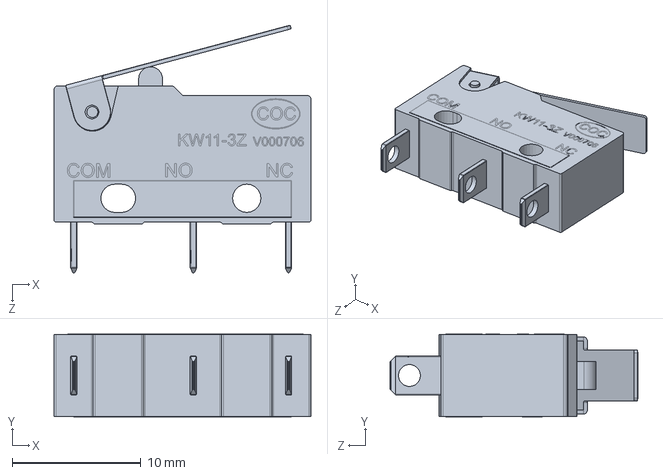
[picture p81: CAD file, 2024-06-11]
Mechanics/Robot´s 3D Models/Componentes/Switchs/Microswitch KW11-3Z-3.SLDPRT
20.0 x 6.44 x 19.3 mm
