franrobots/RescueMaze_FranRobots_WorldWide/Mechanics/Robot´s 3D Models/Disparador/Disparador Tapete/Eixo Biela.SLDPRT

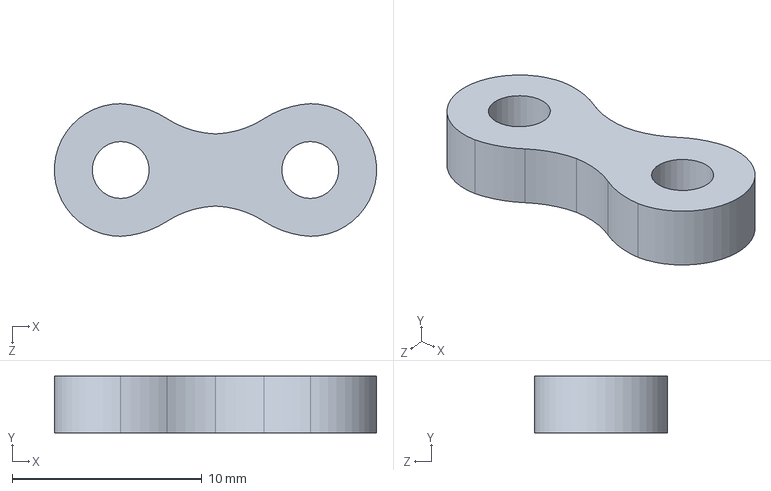
[picture p82: CAD file, 2024-06-19]
Mechanics/Robot´s 3D Models/Disparador/Disparador Tapete/Eixo Biela.SLDPRT
17.0 x 3.00 x 7.00 mm
