franrobots/RescueMaze_FranRobots_WorldWide/Mechanics/Robot´s 3D Models/Peça Frente Cima - Maze.SLDPRT

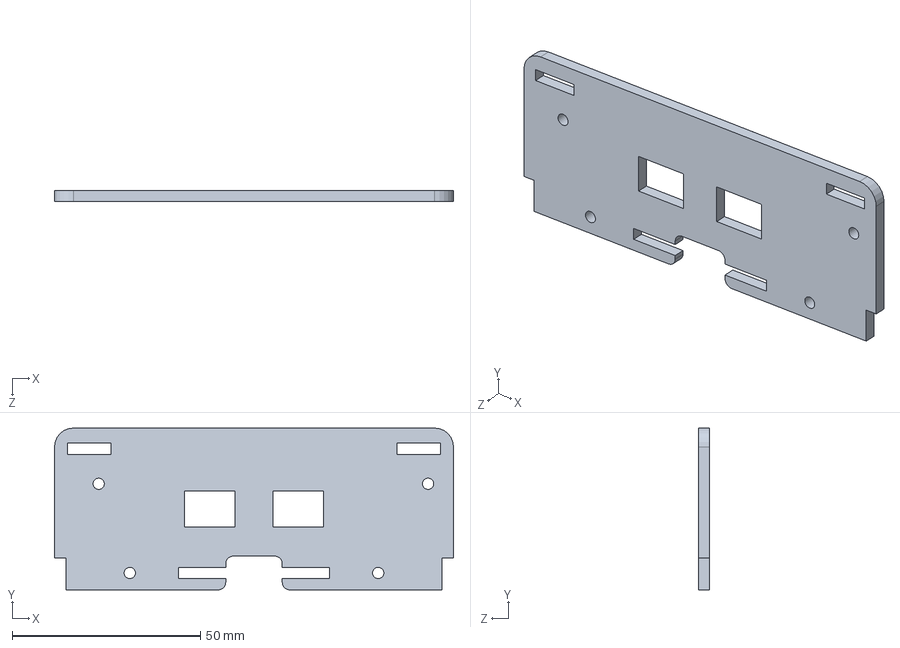
[picture p84: CAD file, 2024-06-19]
Mechanics/Robot´s 3D Models/Peça Frente Cima - Maze.SLDPRT
106.0 x 43.0 x 3.00 mm
