franrobots/RescueMaze_FranRobots_WorldWide/Mechanics/Robot´s 3D Models/Rodas e esteiras/Rodas/7988 - Atual/Engrenagem Motora Reduzida - Passo 11,92 7988.SLDPRT

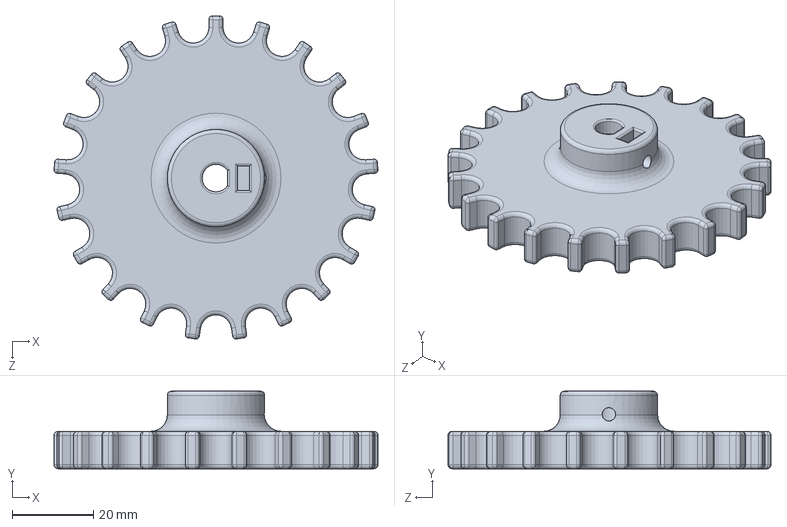
[picture p85: CAD file, 2024-06-19]
Mechanics/Robot´s 3D Models/Rodas e esteiras/Rodas/7988 - Atual/Engrenagem Motora Reduzida - Passo 11,92 7988.SLDPRT
79.8 x 19.1 x 79.6 mm
