franrobots/RescueMaze_FranRobots_WorldWide/Mechanics/Robot´s 3D Models/Andar Base - Maze.SLDPRT

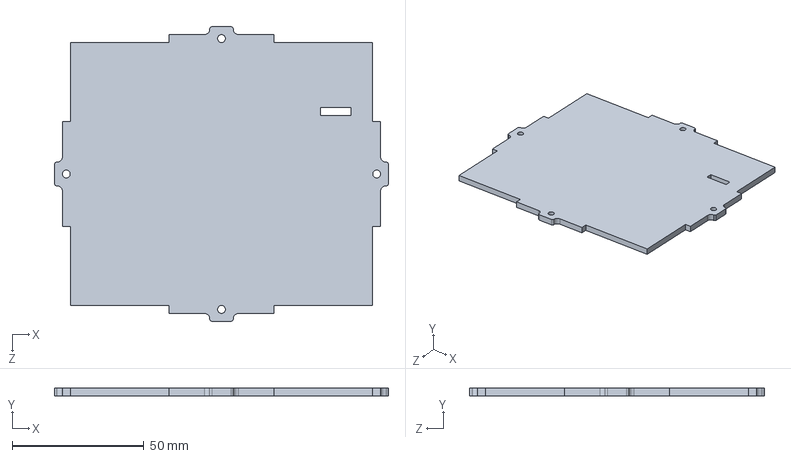
[picture p86: CAD file, 2024-06-19]
Mechanics/Robot´s 3D Models/Andar Base - Maze.SLDPRT
127.0 x 3.00 x 112.0 mm
