franrobots/RescueMaze_FranRobots_WorldWide/Mechanics/Robot´s 3D Models/Componentes/GY-VL53/GY-VL53L1XV2.SLDPRT

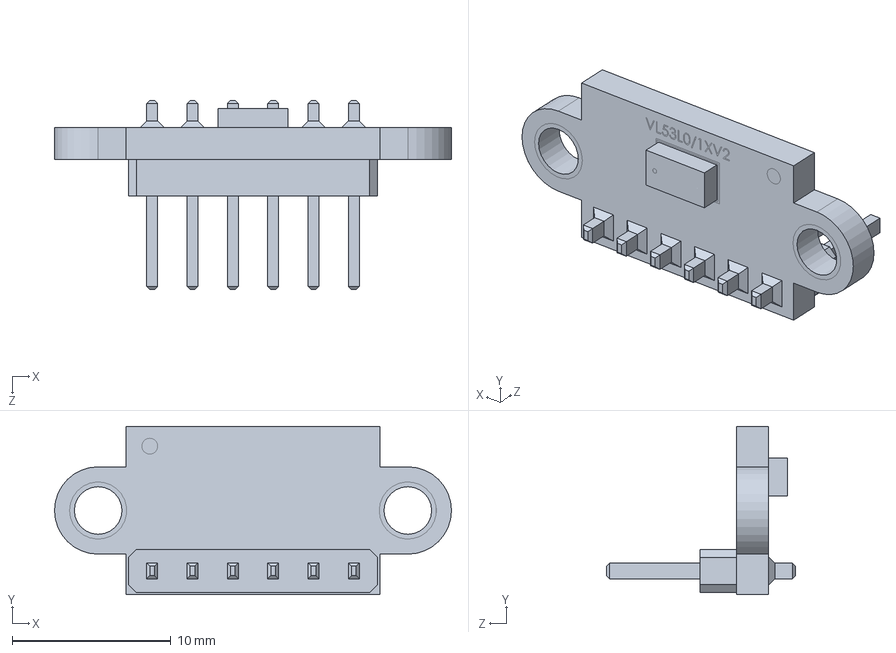
[picture p87: CAD file, 2024-06-19]
Mechanics/Robot´s 3D Models/Componentes/GY-VL53/GY-VL53L1XV2.SLDPRT
25.0 x 10.6 x 11.9 mm
