franrobots/RescueMaze_FranRobots_WorldWide/Mechanics/Robot´s 3D Models/Componentes/Placa de Refletância/Case LDR Sobrepor.SLDPRT

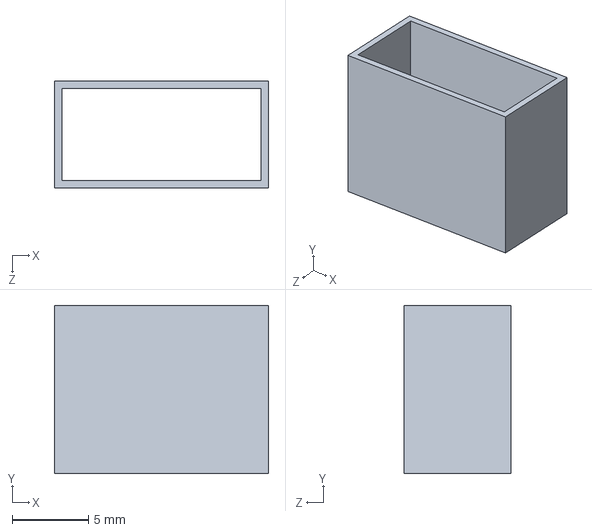
[picture p88: CAD file, 2024-06-14]
Mechanics/Robot´s 3D Models/Componentes/Placa de Refletância/Case LDR Sobrepor.SLDPRT
14.0 x 11.0 x 7.00 mm
