franrobots/RescueMaze_FranRobots_WorldWide/Mechanics/Robot´s 3D Models/Disparador/Disparador Tapete/Émbolo Tapete Disparador.SLDPRT

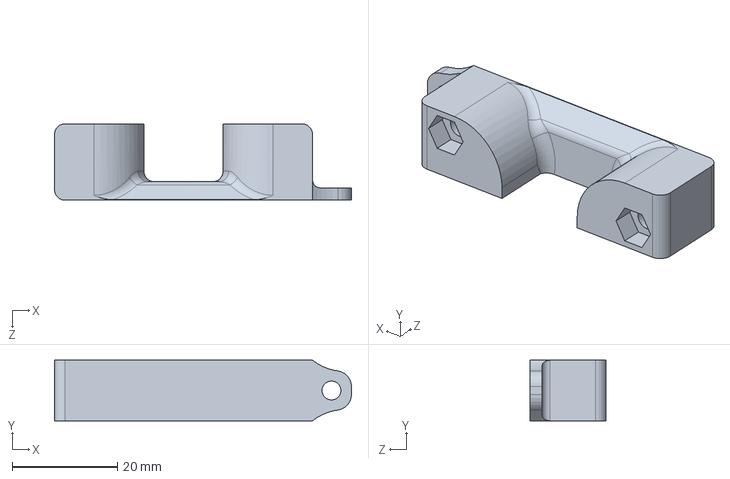
[picture p89: CAD file, 2024-06-19]
Mechanics/Robot´s 3D Models/Disparador/Disparador Tapete/Émbolo Tapete Disparador.SLDPRT
56.4 x 11.5 x 14.5 mm
