franrobots/RescueMaze_FranRobots_WorldWide/Mechanics/Robot´s 3D Models/Disparador/Estoque Disparador/Tampa - Estoque Disparador.SLDPRT

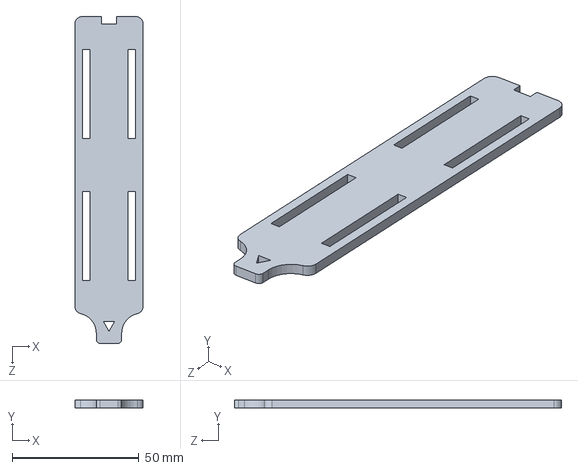
[picture p90: CAD file, 2024-06-19]
Mechanics/Robot´s 3D Models/Disparador/Estoque Disparador/Tampa - Estoque Disparador.SLDPRT
27.0 x 3.00 x 129.0 mm
