franrobots/RescueMaze_FranRobots_WorldWide/Mechanics/Robot´s 3D Models/Peça AntiCapotamento.SLDPRT

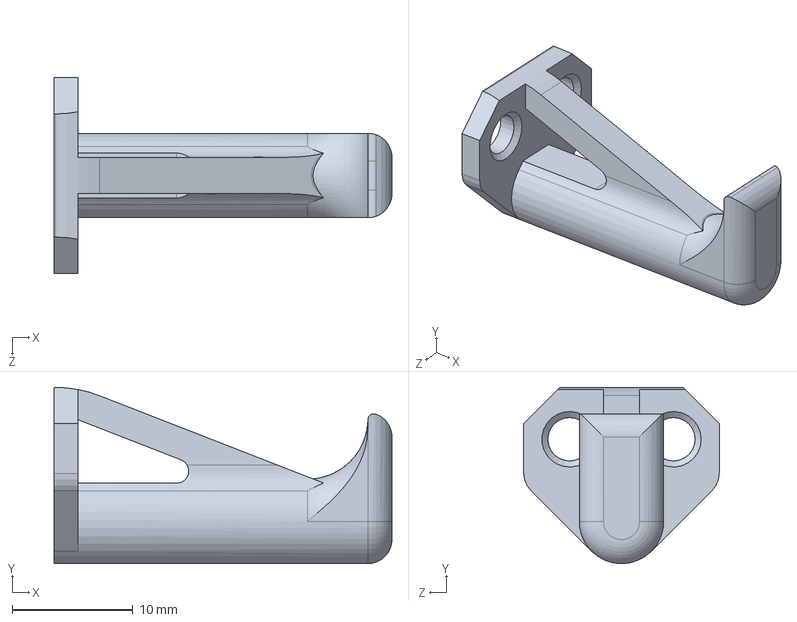
[picture p92: CAD file, 2024-06-19]
Mechanics/Robot´s 3D Models/Peça AntiCapotamento.SLDPRT
28.0 x 14.6 x 16.2 mm
