franrobots/RescueMaze_FranRobots_WorldWide/Mechanics/Robot´s 3D Models/Disparador/Estoque Disparador/Tampa Superior - Estoque Disparador.SLDPRT

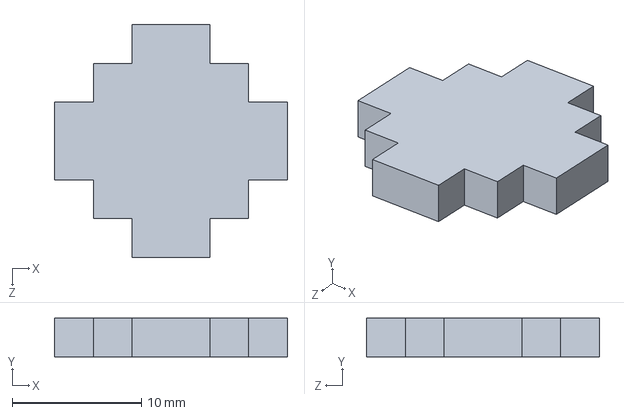
[picture p93: CAD file, 2024-06-11]
Mechanics/Robot´s 3D Models/Disparador/Estoque Disparador/Tampa Superior - Estoque Disparador.SLDPRT
18.0 x 3.00 x 18.0 mm
