franrobots/RescueMaze_FranRobots_WorldWide/Mechanics/Robot´s 3D Models/Peça Trás - Maze.SLDPRT

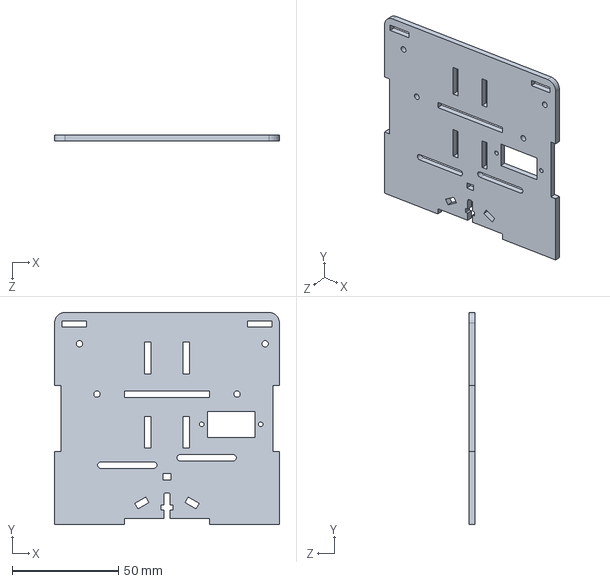
[picture p94: CAD file, 2024-06-19]
Mechanics/Robot´s 3D Models/Peça Trás - Maze.SLDPRT
106.0 x 100.0 x 3.00 mm
