franrobots/RescueMaze_FranRobots_WorldWide/Mechanics/Robot´s 3D Models/Teto - Robô Maze.SLDPRT

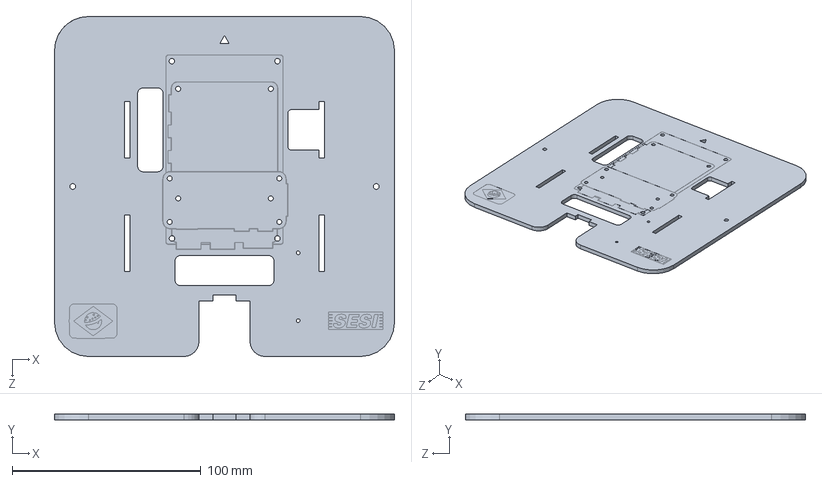
[picture p95: CAD file, 2024-06-19]
Mechanics/Robot´s 3D Models/Teto - Robô Maze.SLDPRT
180.0 x 3.00 x 180.0 mm
