franrobots/RescueMaze_FranRobots_WorldWide/Mechanics/Robot´s 3D Models/Andar Principal - Maze.SLDPRT

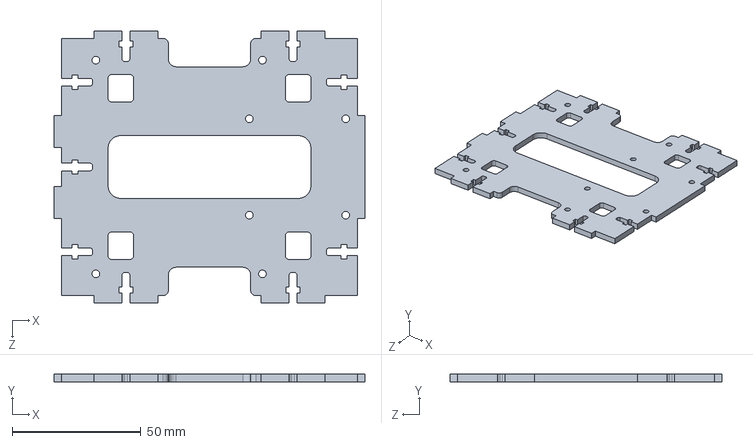
[picture p96: CAD file, 2024-06-19]
Mechanics/Robot´s 3D Models/Andar Principal - Maze.SLDPRT
121.0 x 3.00 x 106.0 mm
