franrobots/RescueMaze_FranRobots_WorldWide/Mechanics/Robot´s 3D Models/Peça Frente Baixo - Maze.SLDPRT

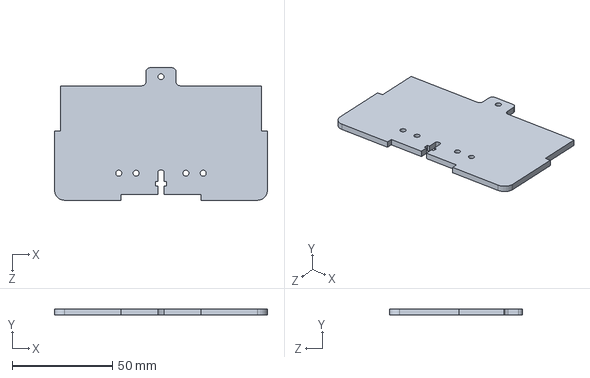
[picture p97: CAD file, 2024-06-19]
Mechanics/Robot´s 3D Models/Peça Frente Baixo - Maze.SLDPRT
106.0 x 3.00 x 66.0 mm
