franrobots/RescueMaze_FranRobots_WorldWide/Mechanics/Robot´s 3D Models/Alça Robô Maze.SLDPRT

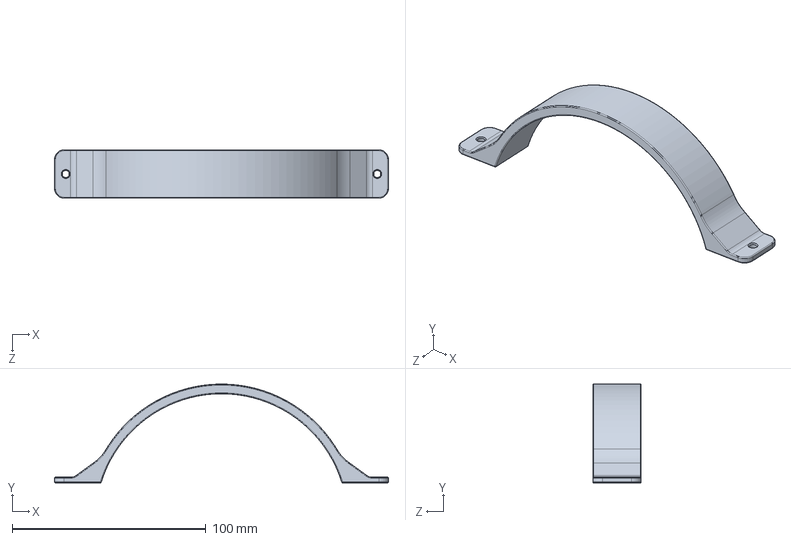
[picture p98: CAD file, 2024-06-11]
Mechanics/Robot´s 3D Models/Alça Robô Maze.SLDPRT
172.3 x 51.0 x 25.0 mm
