franrobots/RescueMaze_FranRobots_WorldWide/Electronics/Media/MotherBoard/TeamMember_Soldering_NewBoard.jpeg

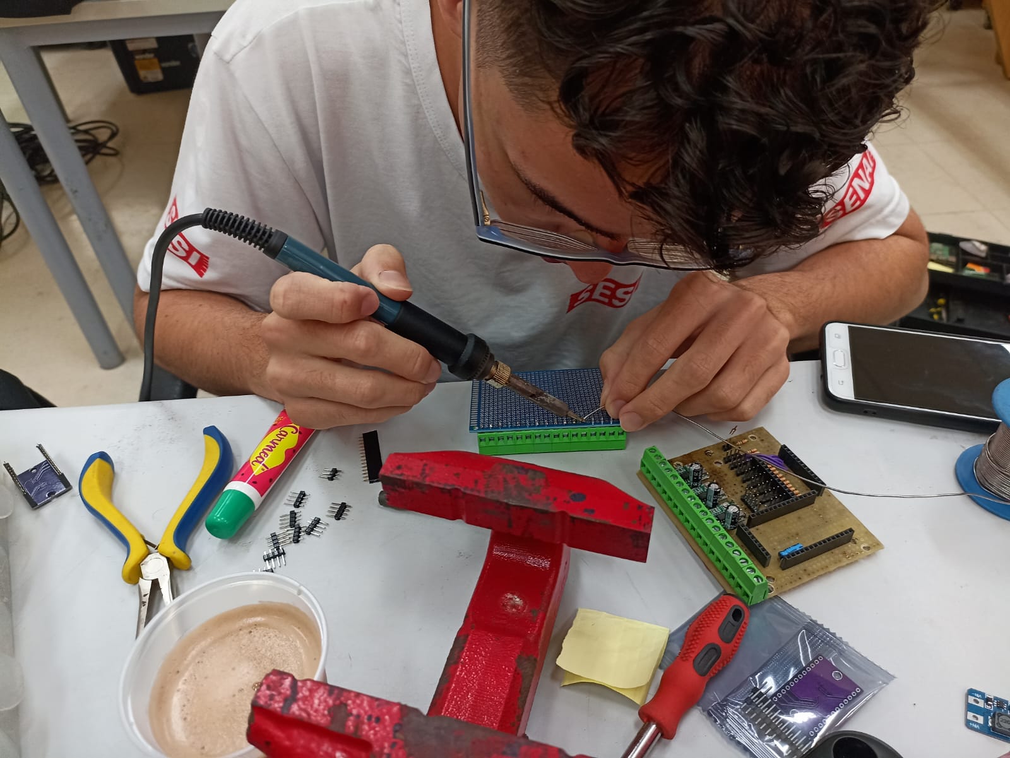
Electronics/Media/MotherBoard/TeamMember_Soldering_NewBoard.jpeg
