franrobots/RescueMaze_FranRobots_WorldWide/Mechanics/3D Printing Prices and Specs./Price and Printing Specs. - 1x Free Gear Wheel - RescueMaze FR.jpg

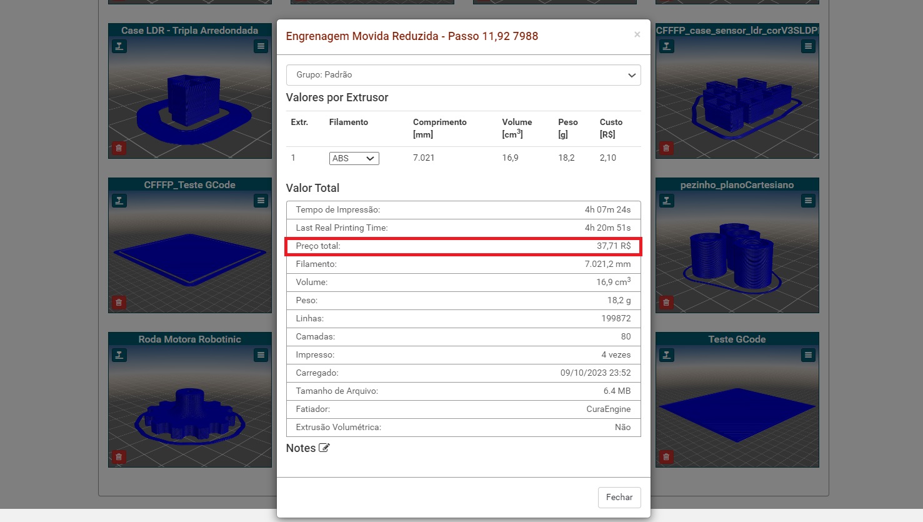
Mechanics/3D Printing Prices and Specs./Price and Printing Specs. - 1x Free Gear Wheel - RescueMaze FR.jpg
