franrobots/RescueMaze_FranRobots_WorldWide/Mechanics/Media/3D/3D_Printer_Website.jpeg

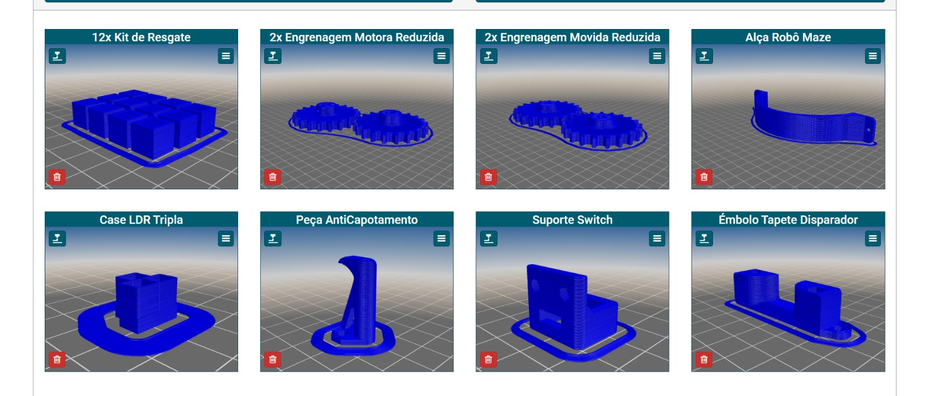
Mechanics/Media/3D/3D_Printer_Website.jpeg
