franrobots/RescueMaze_FranRobots_WorldWide/Mechanics/Media/3D/Isometric_Print_Robot.jpeg

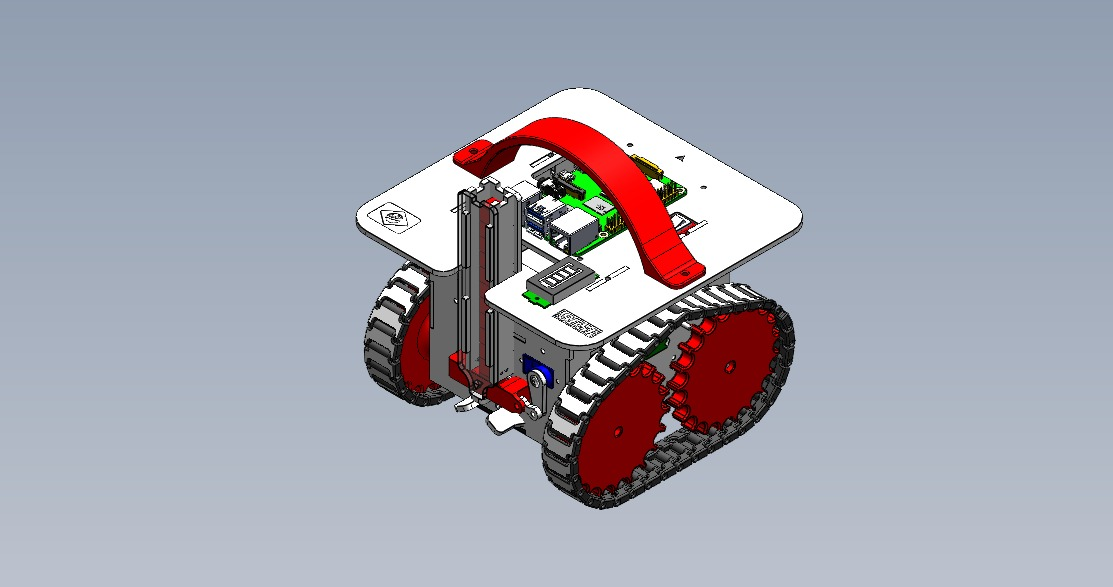
Mechanics/Media/3D/Isometric_Print_Robot.jpeg
