franrobots/RescueMaze_FranRobots_WorldWide/Mechanics/Media/3D/TrackTeeth_3D_Printing_Slicer.jpeg

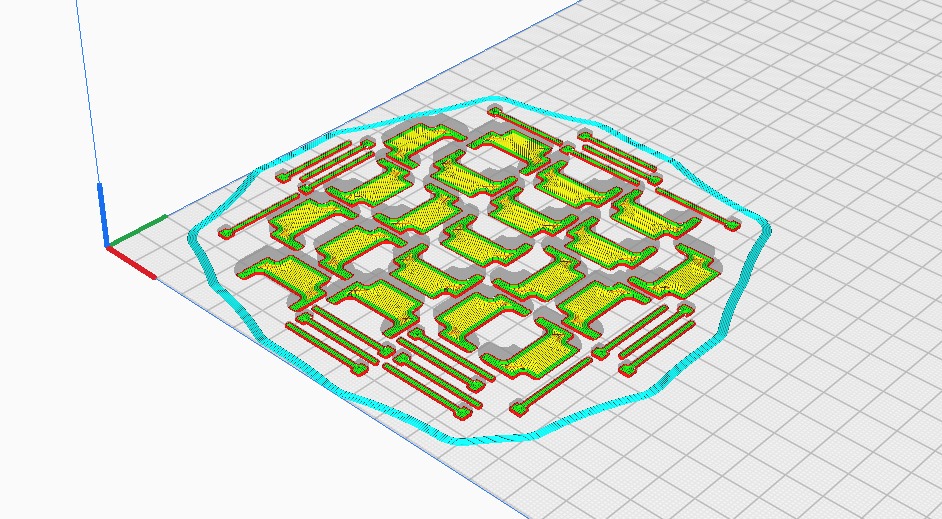
Mechanics/Media/3D/TrackTeeth_3D_Printing_Slicer.jpeg
